adouglas89/Big-Quiet-Fan/dfm v1.0/stl v2/framesecondary_secondarybladeshollow.stl

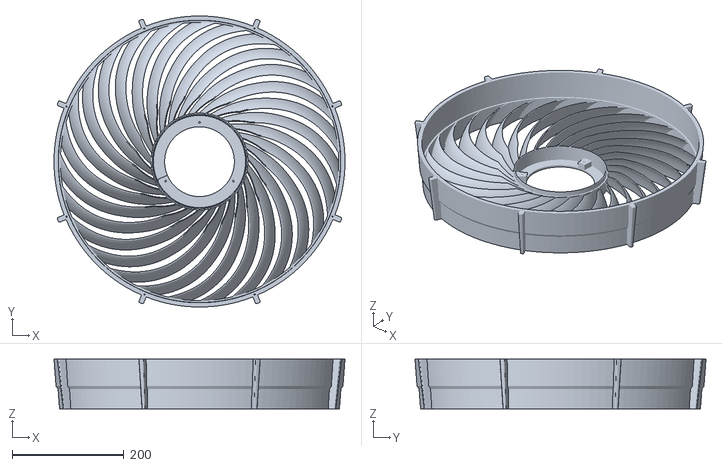
[picture p14: CAD file, 2025-12-09]
dfm v1.0/stl v2/framesecondary_secondarybladeshollow.stl
520.8 x 520.8 x 88.8
