adouglas89/Big-Quiet-Fan/dfm v1.0/trimmedprimarynorim.step

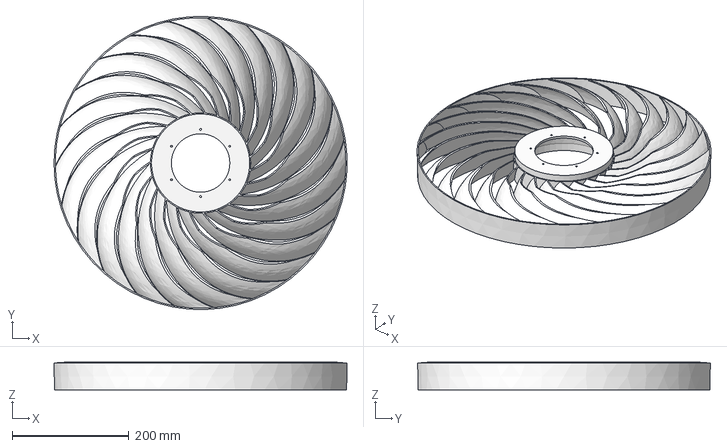
[picture p15: CAD file, 2026-05-13]
dfm v1.0/trimmedprimarynorim.step
502.3 x 502.4 x 47.4 mm
