adouglas89/Big-Quiet-Fan/ul507shortfatfingerprobe.stl

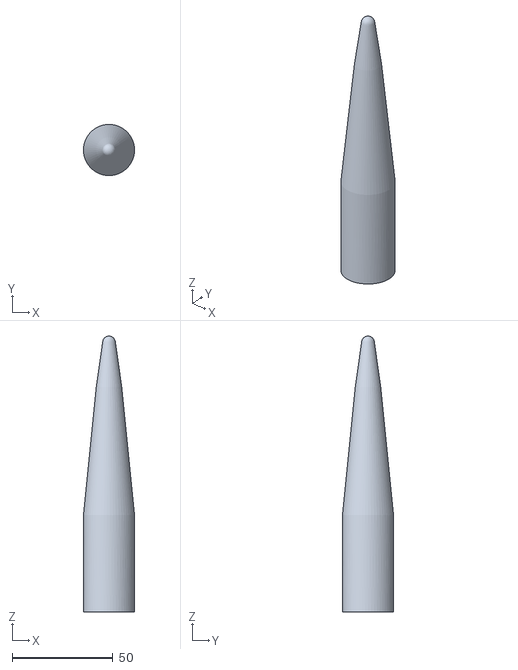
[picture p16: CAD file, 2026-04-09]
ul507shortfatfingerprobe.stl
25.4 x 25.4 x 137.0
