adouglas89/Big-Quiet-Fan/dfm v1.0/primary_thin_blades_norimstillholes.step

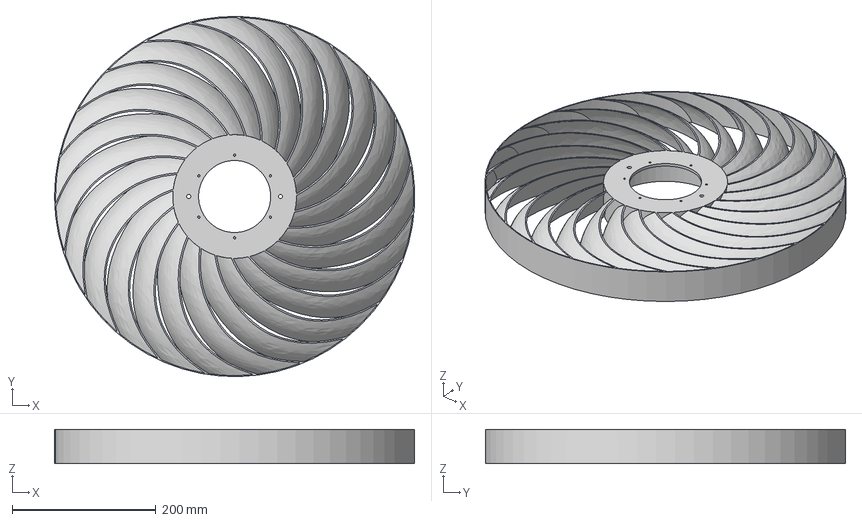
[picture p17: CAD file, 2026-05-13]
dfm v1.0/primary_thin_blades_norimstillholes.step
500.6 x 500.8 x 47.4 mm
