adouglas89/Big-Quiet-Fan/dfm v1.0/prototyping stuff/3mf/finished for kits run june 13 onwards/motor_cover_jayohsblackpetg1.3mf

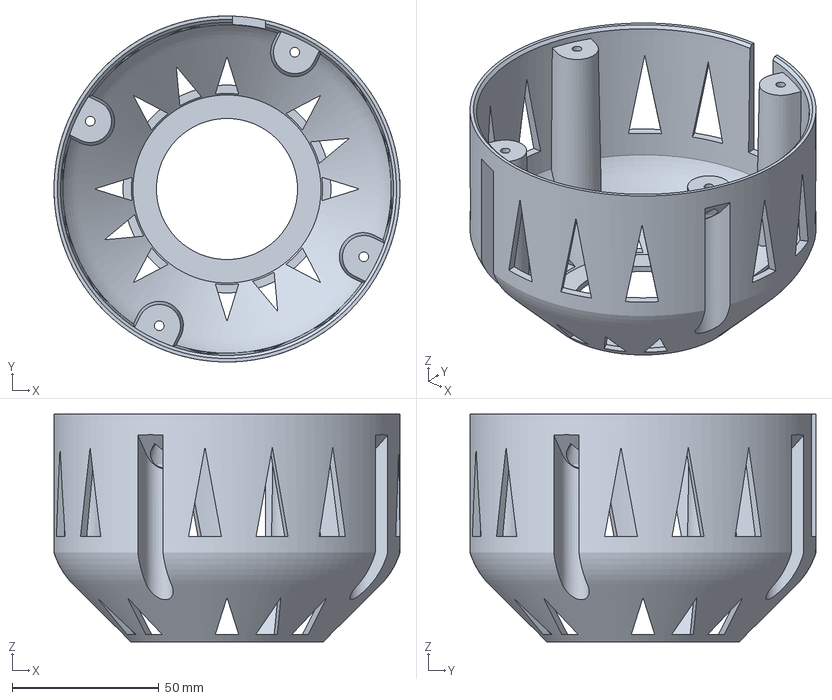
[picture p18: CAD file, 2026-06-17]
dfm v1.0/prototyping stuff/3mf/finished for kits run june 13 onwards/motor_cover_jayohsblackpetg1.3mf
117.7 x 117.7 x 77.5 mm
