adouglas89/Big-Quiet-Fan/dfm v1.0/prototyping stuff/3mf/veho-600/fishnet_clamp_ringtry1-hsjayopet-1mmnozzle-june18_2026.3mf

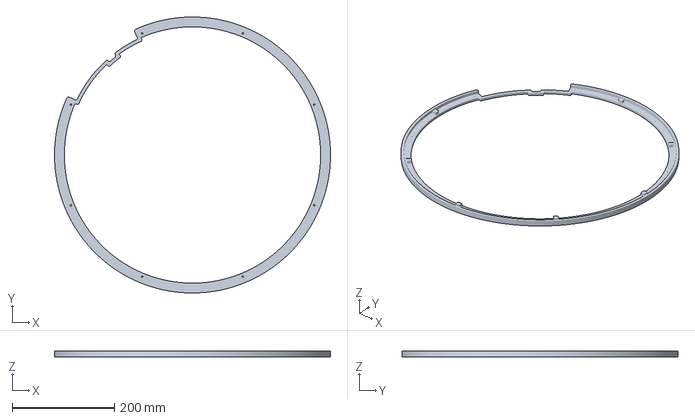
[picture p19: CAD file, 2026-06-18]
dfm v1.0/prototyping stuff/3mf/veho-600/fishnet_clamp_ringtry1-hsjayopet-1mmnozzle-june18_2026.3mf
539.9 x 539.9 x 11.0 mm
