adouglas89/Big-Quiet-Fan/dfm v1.0/prototyping stuff/3mf/veho-600/pretty good/secondary moddedforv-series-1mmnozzle-petgsplit6_wasgood tweakedtravelbeforeretractlimit.3mf

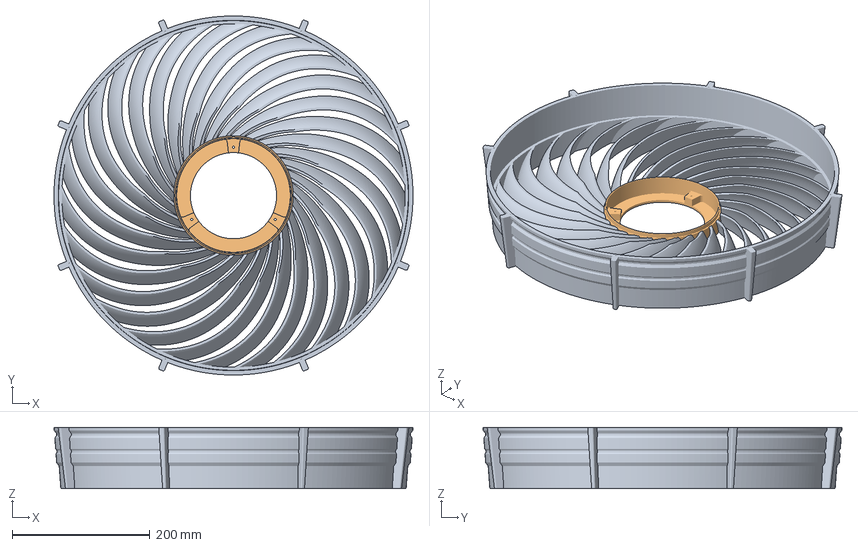
[picture p20: CAD file, 2026-06-16]
dfm v1.0/prototyping stuff/3mf/veho-600/pretty good/secondary moddedforv-series-1mmnozzle-petgsplit6_wasgood tweakedtravelbeforeretractlimit.3mf
520.9 x 520.9 x 88.8 mm
secondary-framesecondaryprintable_outersplittry2.stl
secondary-framesecondaryprintablecentersplittry2.stl
