adouglas89/Big-Quiet-Fan/dfm v1.0/prototyping stuff/stls/new_coupler3/flywheel nointernalholescaptivetype.stl

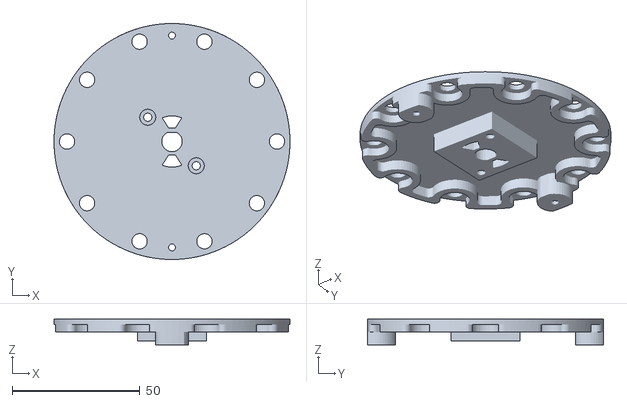
[picture p21: CAD file, 2025-12-23]
dfm v1.0/prototyping stuff/stls/new_coupler3/flywheel nointernalholescaptivetype.stl
92.2 x 92.2 x 10.0
