adouglas89/Big-Quiet-Fan/dfm v1.0/prototyping stuff/stls/simplificationexperiment/plate.stl

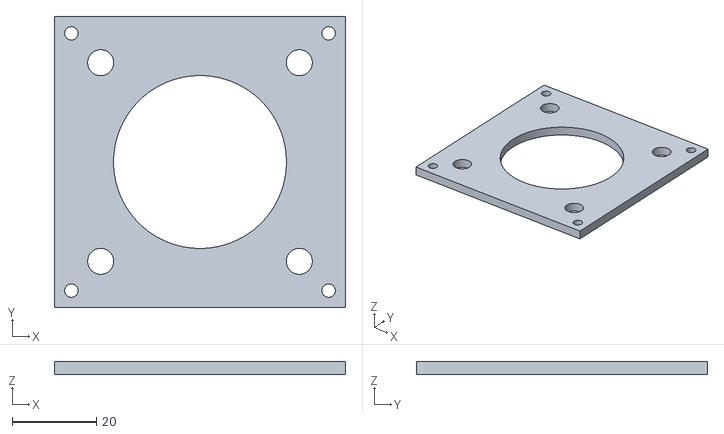
[picture p22: CAD file, 2026-01-07]
dfm v1.0/prototyping stuff/stls/simplificationexperiment/plate.stl
69.0 x 69.0 x 3.00
