adouglas89/Big-Quiet-Fan/dfm v1.0/stl v2/supportblockerfor primary.stl

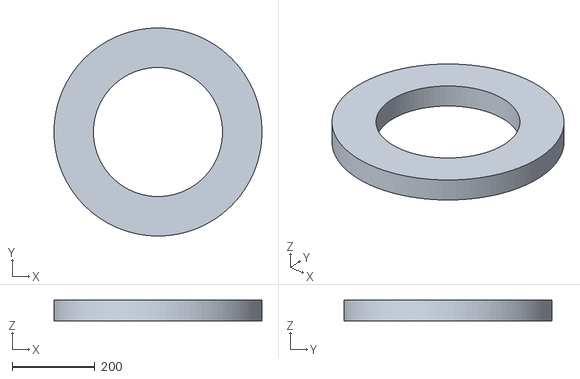
[picture p23: CAD file, 2025-12-06]
dfm v1.0/stl v2/supportblockerfor primary.stl
501.9 x 501.9 x 50.0
