adouglas89/Big-Quiet-Fan/dfm v1.0/prototyping stuff/3mf/finished for kits run june 13 onwards/threearmedcouplerallthreepieces_june15_2026.3mf

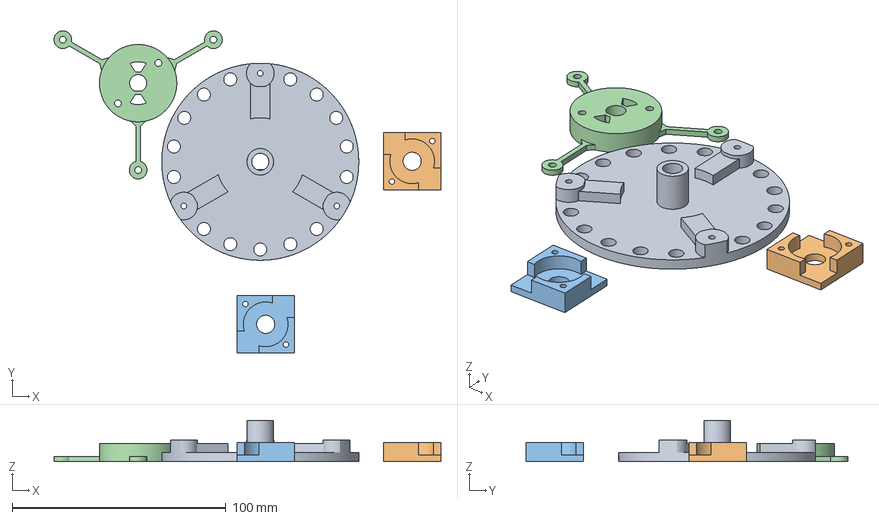
[picture p24: CAD file, 2026-06-17]
dfm v1.0/prototyping stuff/3mf/finished for kits run june 13 onwards/threearmedcouplerallthreepieces_june15_2026.3mf
181.1 x 150.8 x 19.3 mm
bladesideflywheelthreearm.stl
coupler captivething mirror.stl
coupler captivething.stl
motorsidecouplerthreearm9.stl
