adouglas89/Big-Quiet-Fan/dfm v1.0/prototyping stuff/bladetry4.stl

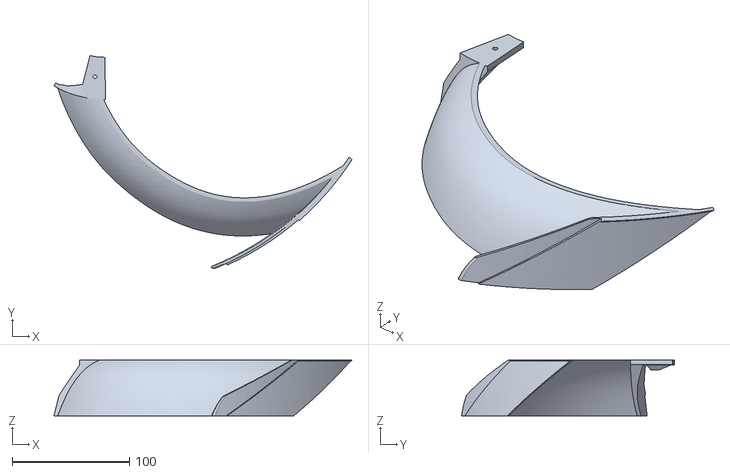
[picture p25: CAD file, 2026-04-09]
dfm v1.0/prototyping stuff/bladetry4.stl
254.3 x 181.6 x 47.4
