adouglas89/Big-Quiet-Fan/dfm v1.0/prototyping stuff/stls/modifierforclamp.stl

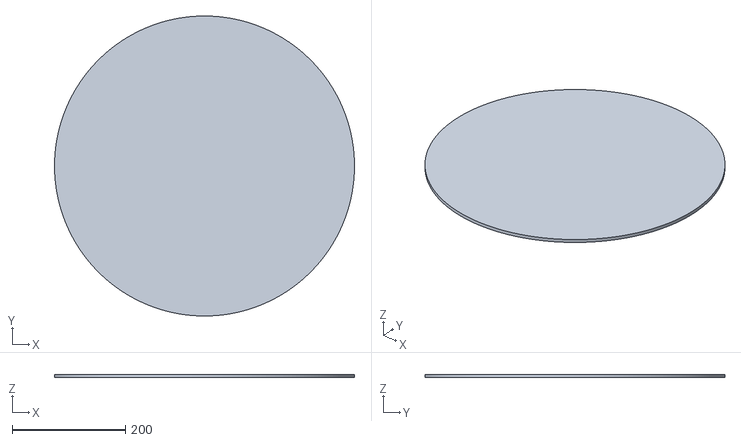
[picture p26: CAD file, 2026-06-18]
dfm v1.0/prototyping stuff/stls/modifierforclamp.stl
529.7 x 529.7 x 6.00
