adouglas89/Big-Quiet-Fan/dfm v1.0/prototyping stuff/stls/simplificationexperiment/pla_motormount.stl

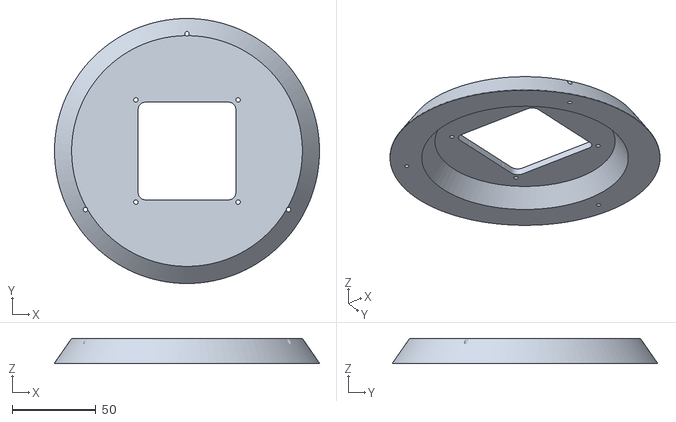
[picture p27: CAD file, 2026-01-07]
dfm v1.0/prototyping stuff/stls/simplificationexperiment/pla_motormount.stl
158.3 x 158.2 x 15.2
