adouglas89/Big-Quiet-Fan/dfm v1.0/prototyping stuff/3mf/finished for kits run june 13 onwards/electronicscoverpetg_0.6_trying to get working3.3mf

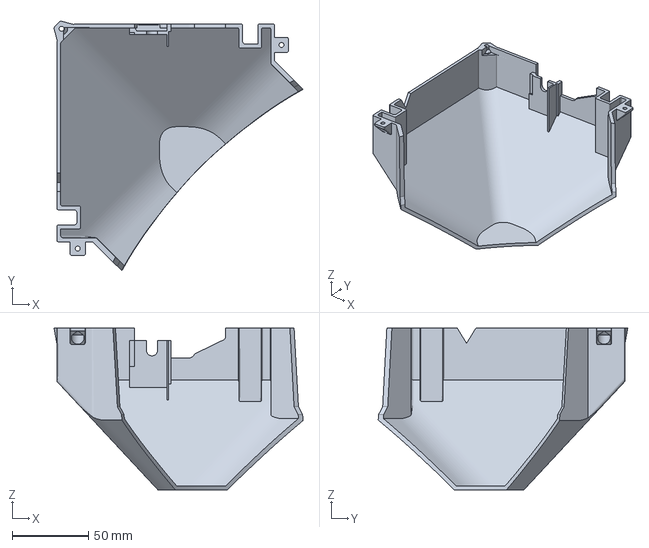
[picture p28: CAD file, 2026-06-17]
dfm v1.0/prototyping stuff/3mf/finished for kits run june 13 onwards/electronicscoverpetg_0.6_trying to get working3.3mf
163.5 x 163.9 x 106.2 mm
