adouglas89/Big-Quiet-Fan/dfm v1.0/prototyping stuff/bladetry9.stl

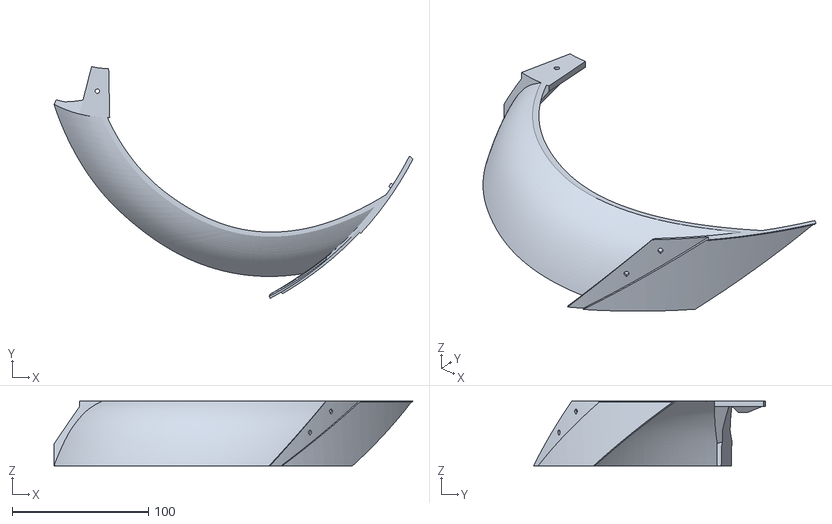
[picture p29: CAD file, 2026-04-09]
dfm v1.0/prototyping stuff/bladetry9.stl
263.4 x 170.1 x 47.4
