adouglas89/Big-Quiet-Fan/dfm v1.0/prototyping stuff/stls/peg5.stl

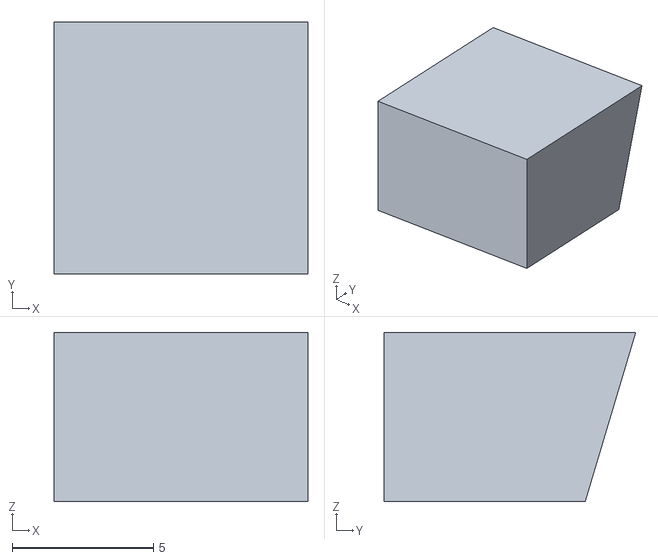
[picture p30: CAD file, 2026-06-18]
dfm v1.0/prototyping stuff/stls/peg5.stl
9.00 x 8.91 x 6.00
