adouglas89/Big-Quiet-Fan/dfm v1.0/prototyping stuff/stls/new_coupler3/backcapturethingcoupler.stl

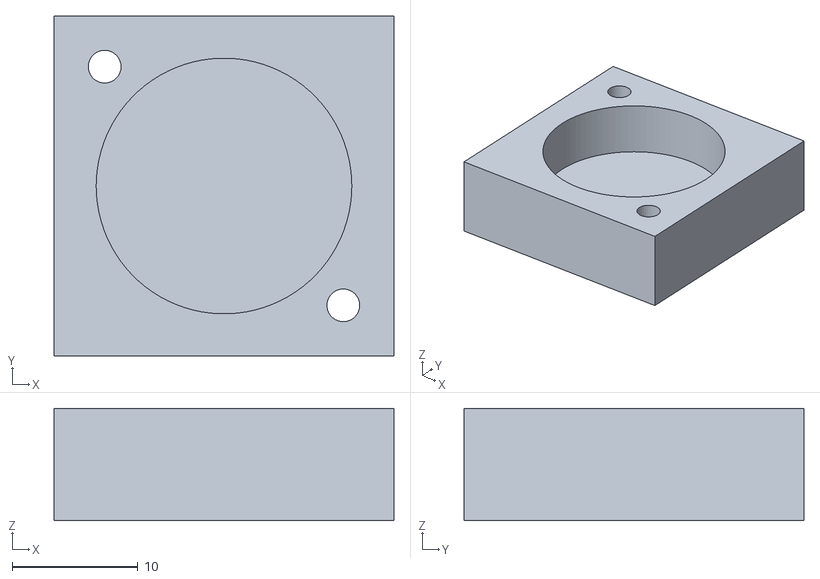
[picture p31: CAD file, 2025-12-23]
dfm v1.0/prototyping stuff/stls/new_coupler3/backcapturethingcoupler.stl
27.0 x 27.0 x 8.90
