adouglas89/Big-Quiet-Fan/dfm v1.0/prototyping stuff/3mf/finished for kits run june 13 onwards/bqfmotorflexure_3x_85A_june15_2026.3mf

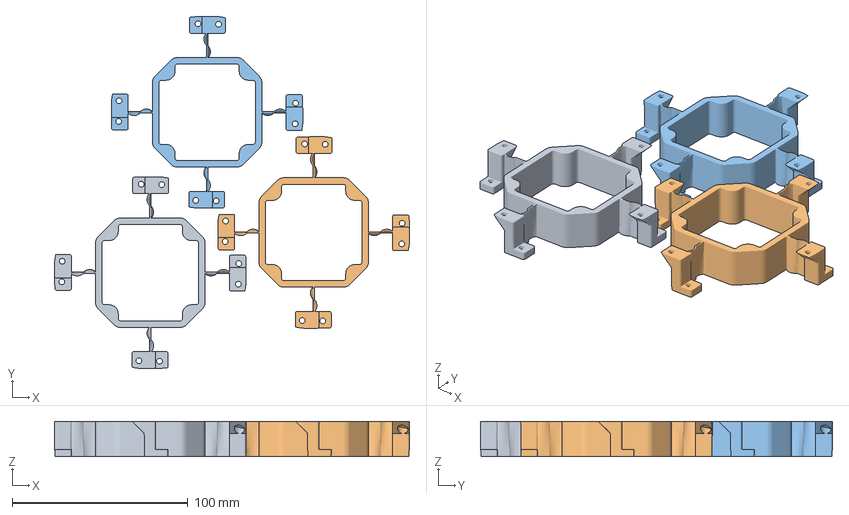
[picture p32: CAD file, 2026-06-16]
dfm v1.0/prototyping stuff/3mf/finished for kits run june 13 onwards/bqfmotorflexure_3x_85A_june15_2026.3mf
202.3 x 200.6 x 20.0 mm
