adouglas89/Big-Quiet-Fan/dfm v1.0/prototyping stuff/3mf/veho-600/primary_middlechoppedaway_upsidedown_trimmed.3mf

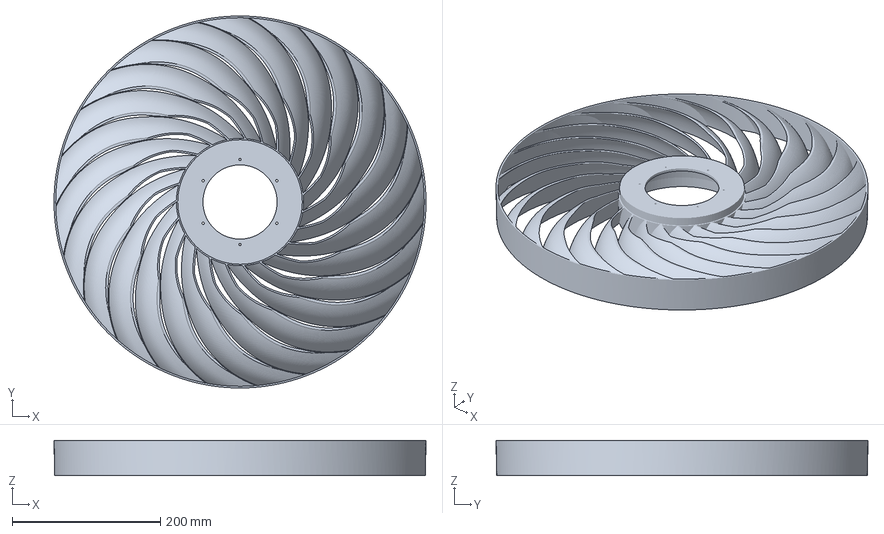
[picture p33: CAD file, 2026-06-16]
dfm v1.0/prototyping stuff/3mf/veho-600/primary_middlechoppedaway_upsidedown_trimmed.3mf
502.6 x 502.6 x 47.4 mm
