adouglas89/Big-Quiet-Fan/dfm v1.0/prototyping stuff/hubtry1.stl

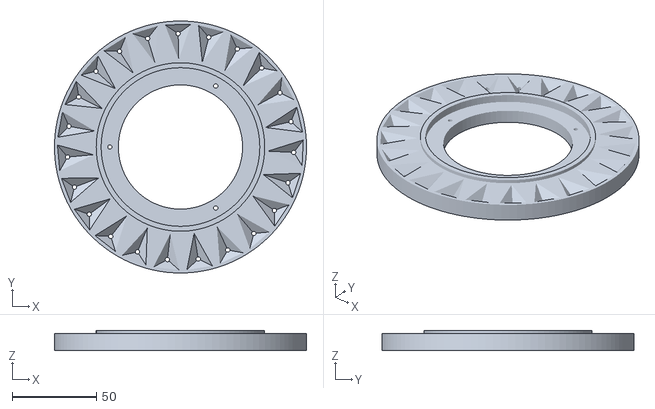
[picture p34: CAD file, 2026-04-09]
dfm v1.0/prototyping stuff/hubtry1.stl
149.3 x 149.3 x 12.0
