adouglas89/Big-Quiet-Fan/dfm v1.0/prototyping stuff/stls/new_coupler3/bladeside.stl

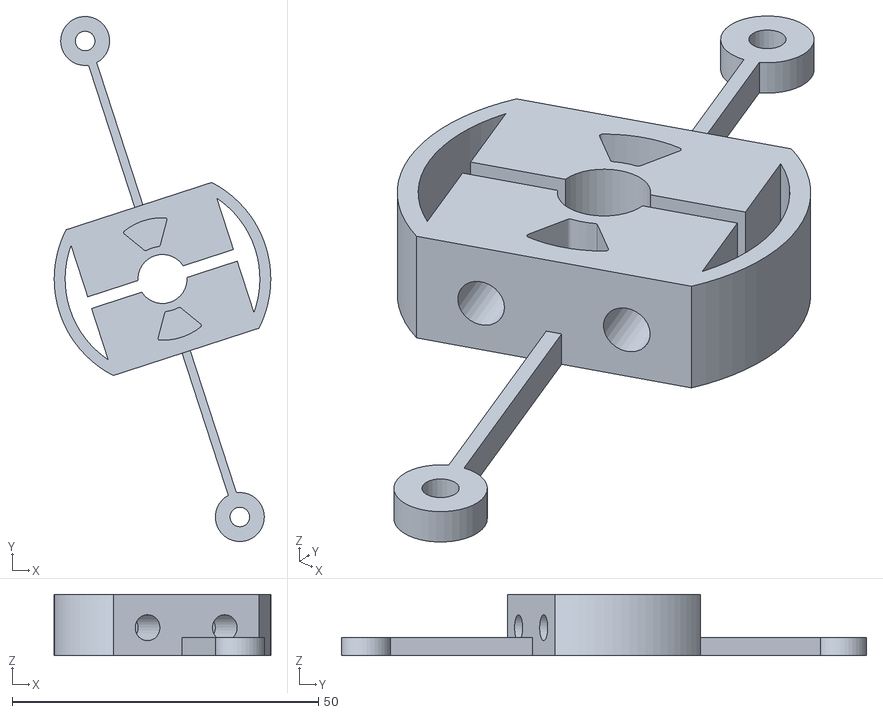
[picture p35: CAD file, 2025-12-23]
dfm v1.0/prototyping stuff/stls/new_coupler3/bladeside.stl
35.4 x 85.7 x 10.0
