adouglas89/Big-Quiet-Fan/dfm v1.0/prototyping stuff/bladetry5.stl

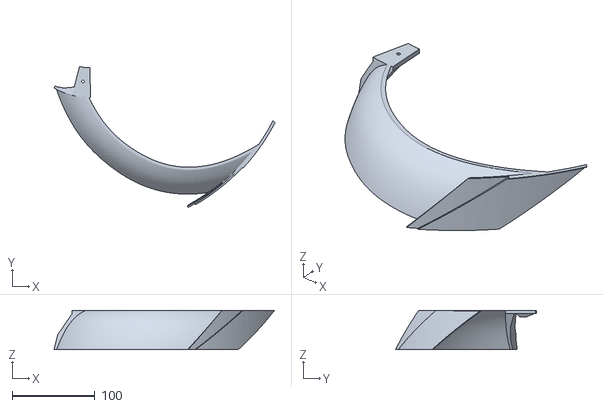
[picture p36: CAD file, 2026-04-09]
dfm v1.0/prototyping stuff/bladetry5.stl
266.5 x 170.1 x 47.4
