adouglas89/Big-Quiet-Fan/dfm v1.0/prototyping stuff/blade.stl

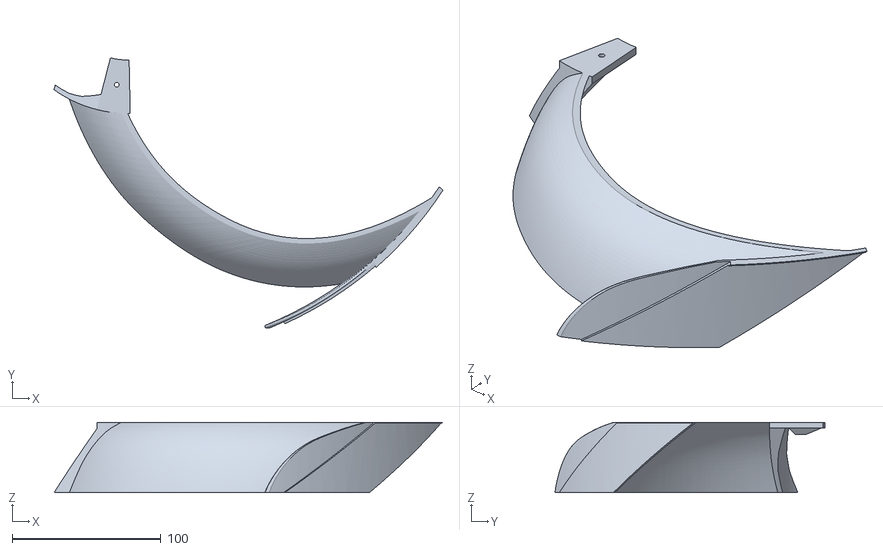
[picture p37: CAD file, 2026-04-09]
dfm v1.0/prototyping stuff/blade.stl
261.5 x 181.6 x 47.4
