adouglas89/Big-Quiet-Fan/dfm v1.0/prototyping stuff/stls/peg3.stl

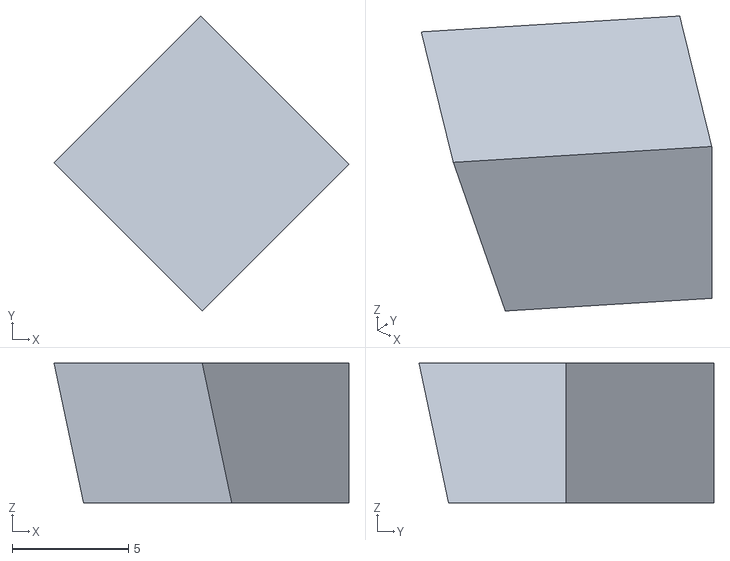
[picture p38: CAD file, 2026-06-18]
dfm v1.0/prototyping stuff/stls/peg3.stl
12.7 x 12.7 x 6.00
