adouglas89/Big-Quiet-Fan/dfm v1.0/prototyping stuff/3mf/electronicscover_petg0_8mm_potrelief.3mf

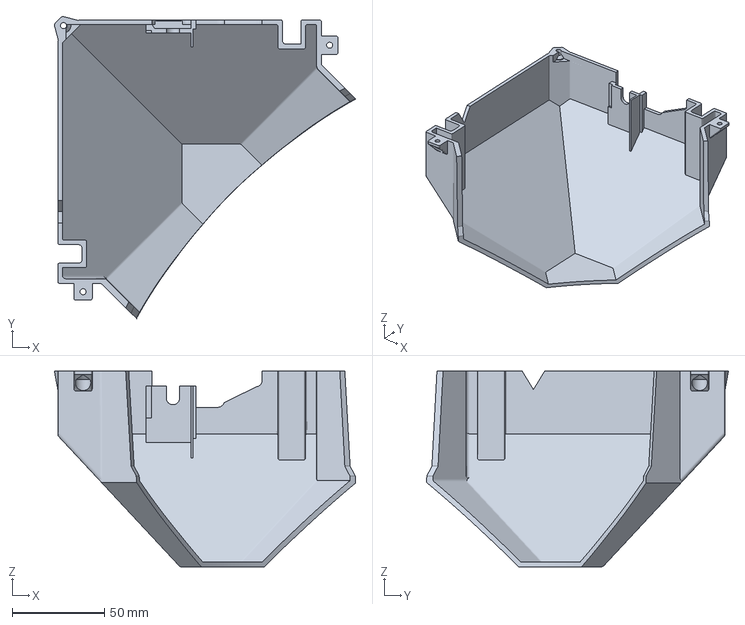
[picture p39: CAD file, 2026-06-16]
dfm v1.0/prototyping stuff/3mf/electronicscover_petg0_8mm_potrelief.3mf
163.5 x 163.9 x 106.2 mm
