adouglas89/Big-Quiet-Fan/dfm v1.0/prototyping stuff/3mf/veho-600/v16p_thin_petg1mmnozzle_thickerlayers.3mf

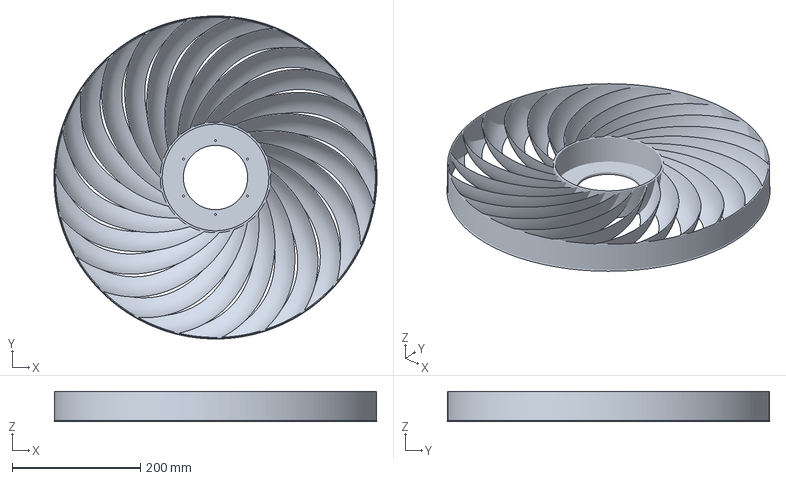
[picture p40: CAD file, 2026-06-16]
dfm v1.0/prototyping stuff/3mf/veho-600/v16p_thin_petg1mmnozzle_thickerlayers.3mf
503.0 x 503.0 x 47.4 mm
