adouglas89/Big-Quiet-Fan/dfm v1.0/prototyping stuff/mangledprimarytry2.stl

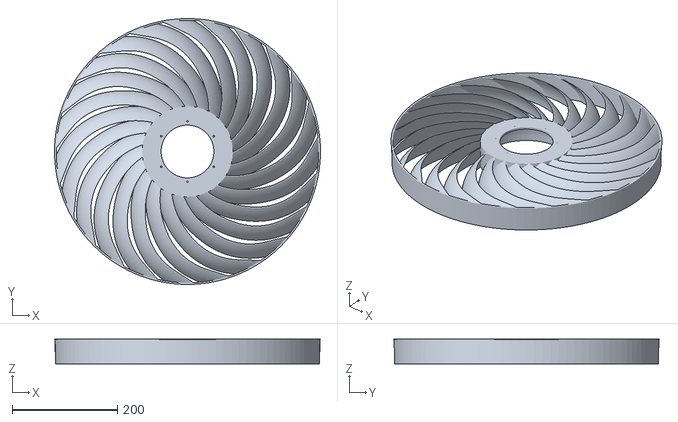
[picture p41: CAD file, 2026-03-26]
dfm v1.0/prototyping stuff/mangledprimarytry2.stl
504.7 x 504.4 x 47.4
