adouglas89/Big-Quiet-Fan/dfm v1.0/prototyping stuff/3mf/electronicscoverpetg_0.6_trying to get working2.3mf

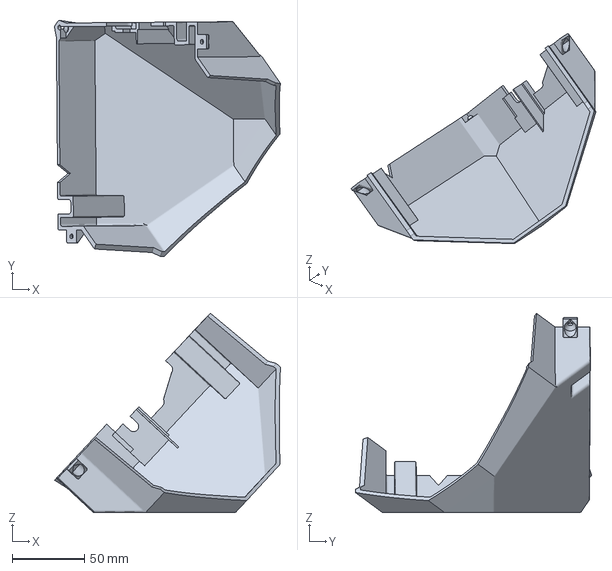
[picture p42: CAD file, 2026-06-16]
dfm v1.0/prototyping stuff/3mf/electronicscoverpetg_0.6_trying to get working2.3mf
156.2 x 163.3 x 137.9 mm
