adouglas89/Big-Quiet-Fan/dfm v1.0/prototyping stuff/3mf/splitblade_center_clamsp_cfpetg_lakegreen.3mf

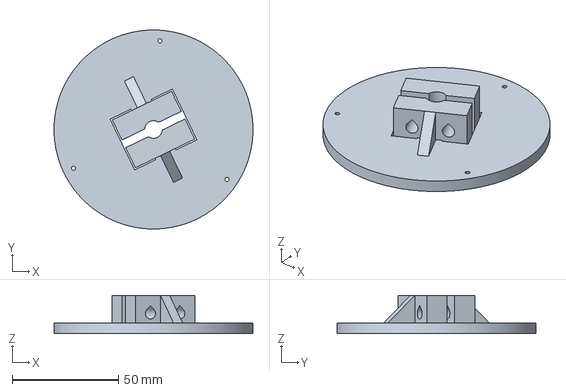
[picture p43: CAD file, 2026-06-16]
dfm v1.0/prototyping stuff/3mf/splitblade_center_clamsp_cfpetg_lakegreen.3mf
93.6 x 93.6 x 18.0 mm
