adouglas89/Big-Quiet-Fan/dfm v1.0/prototyping stuff/stls/pegstry1.stl

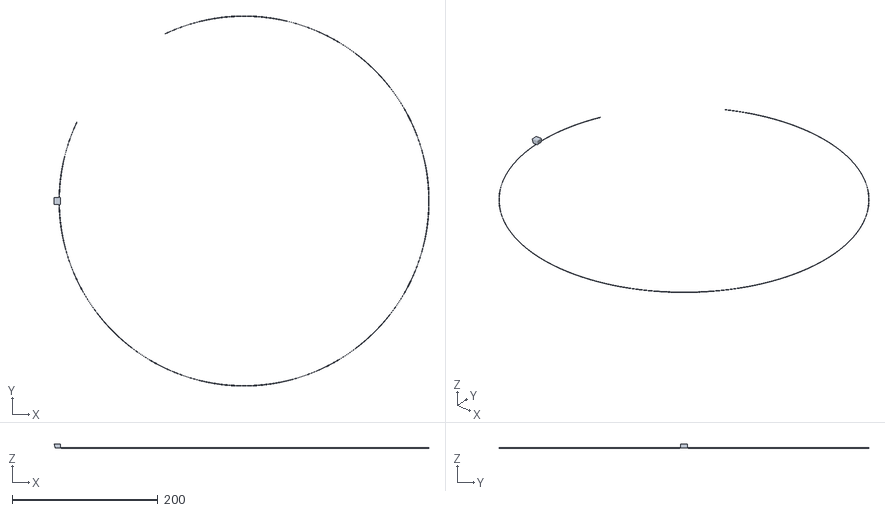
[picture p44: CAD file, 2026-06-18]
dfm v1.0/prototyping stuff/stls/pegstry1.stl
515.3 x 508.3 x 6.00
