adouglas89/Big-Quiet-Fan/dfm v1.0/prototyping stuff/stls/modifierupperpart.stl

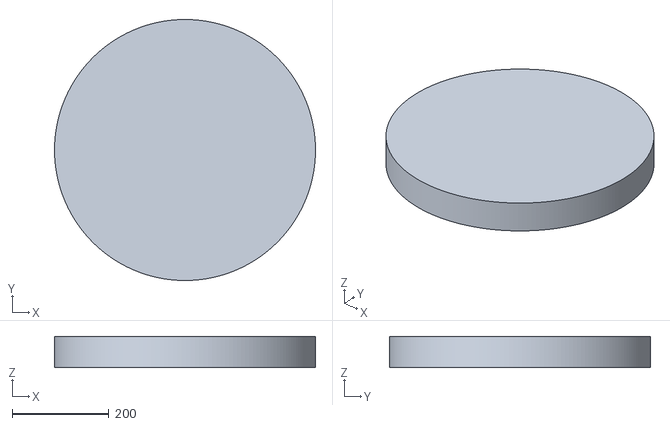
[picture p45: CAD file, 2026-06-17]
dfm v1.0/prototyping stuff/stls/modifierupperpart.stl
539.6 x 539.6 x 64.7
