adouglas89/Big-Quiet-Fan/dfm v1.0/prototyping stuff/3mf/pliersinserttry1.3mf

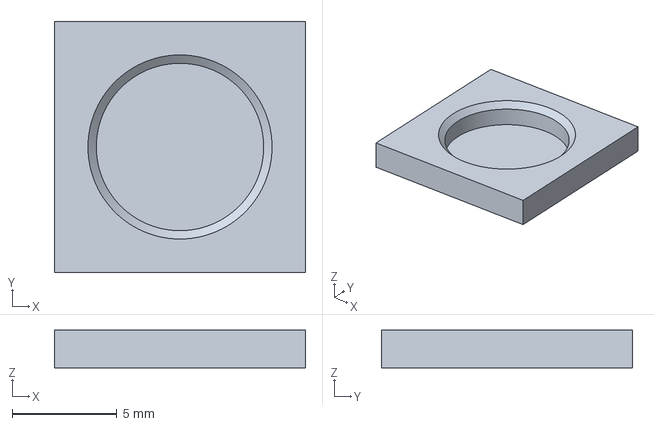
[picture p46: CAD file, 2026-06-16]
dfm v1.0/prototyping stuff/3mf/pliersinserttry1.3mf
12.0 x 12.0 x 1.80 mm
