adouglas89/Big-Quiet-Fan/dfm v1.0/prototyping stuff/stls/motorsidecouplerthreearm_thickenedroot.stl

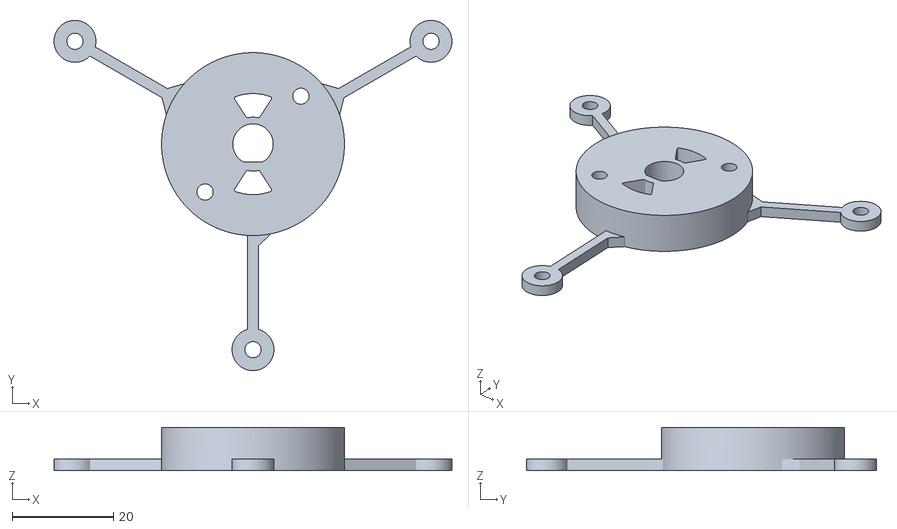
[picture p47: CAD file, 2026-06-16]
dfm v1.0/prototyping stuff/stls/motorsidecouplerthreearm_thickenedroot.stl
78.8 x 69.3 x 8.53
