adouglas89/Big-Quiet-Fan/dfm v1.0/prototyping stuff/stls/secondary-framesecondaryprintable_center_shrunk.stl

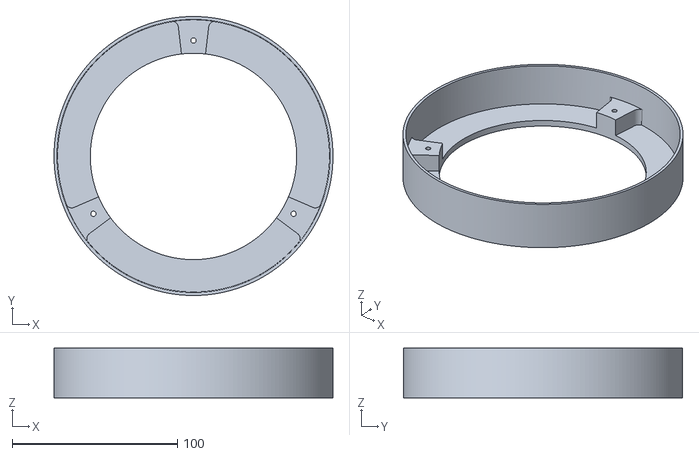
[picture p48: CAD file, 2026-06-16]
dfm v1.0/prototyping stuff/stls/secondary-framesecondaryprintable_center_shrunk.stl
169.0 x 169.0 x 30.2
