adouglas89/Big-Quiet-Fan/dfm v1.0/prototyping stuff/3mf/threearmedcouplerallthreepieces.3mf

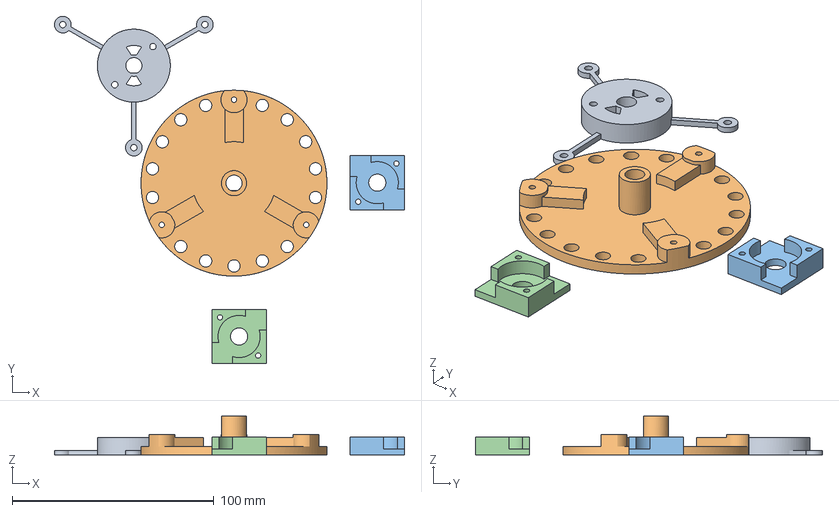
[picture p49: CAD file, 2026-06-16]
dfm v1.0/prototyping stuff/3mf/threearmedcouplerallthreepieces.3mf
173.6 x 172.3 x 19.3 mm
threearmbladesidecorrected.stl
bladesideflywheelthreearm.stl
coupler captivething mirror.stl
coupler captivething.stl
