adouglas89/Big-Quiet-Fan/dfm v1.0/prototyping stuff/stls/modifierforcenterstrength.stl

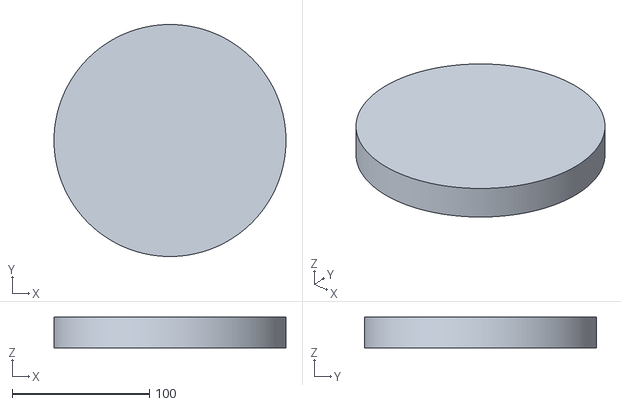
[picture p50: CAD file, 2026-06-16]
dfm v1.0/prototyping stuff/stls/modifierforcenterstrength.stl
169.1 x 169.1 x 22.4
