adouglas89/Big-Quiet-Fan/dfm v1.0/prototyping stuff/3mf/veho-600/secondary_center_thickerforvseries.3mf

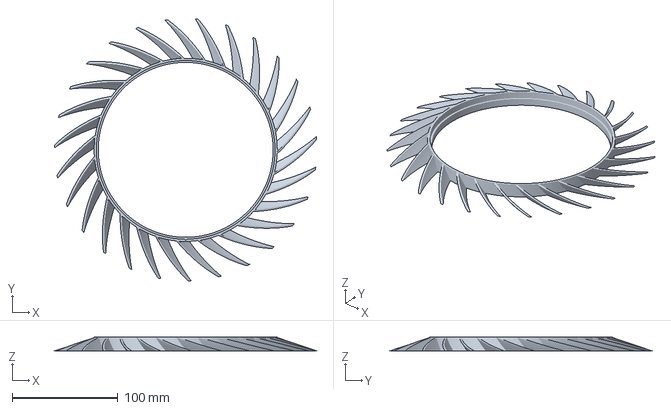
[picture p51: CAD file, 2026-05-19]
dfm v1.0/prototyping stuff/3mf/veho-600/secondary_center_thickerforvseries.3mf
248.0 x 248.1 x 13.0 mm
