adouglas89/Big-Quiet-Fan/dfm v1.0/prototyping stuff/stls/pliersinserttry6.stl

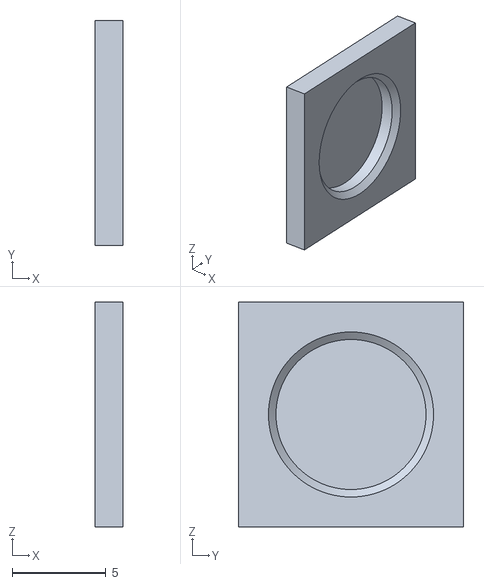
[picture p52: CAD file, 2026-06-16]
dfm v1.0/prototyping stuff/stls/pliersinserttry6.stl
1.50 x 12.0 x 12.0
