adouglas89/Big-Quiet-Fan/dfm v1.0/prototyping stuff/3mf/shaft_clamp_infilled_petgcf_justone.3mf

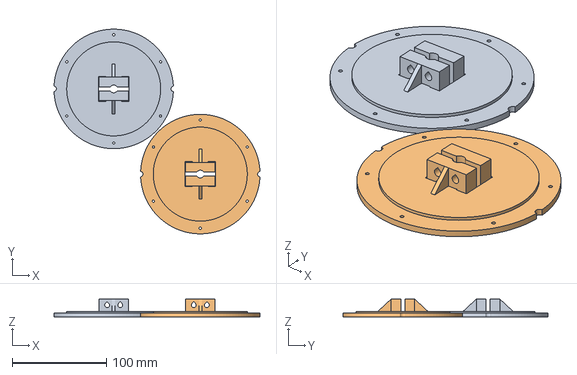
[picture p53: CAD file, 2026-06-16]
dfm v1.0/prototyping stuff/3mf/shaft_clamp_infilled_petgcf_justone.3mf
218.7 x 217.3 x 19.0 mm
