adouglas89/Big-Quiet-Fan/dfm v1.0/prototyping stuff/3mf/splitbladetry2hubouterside.3mf

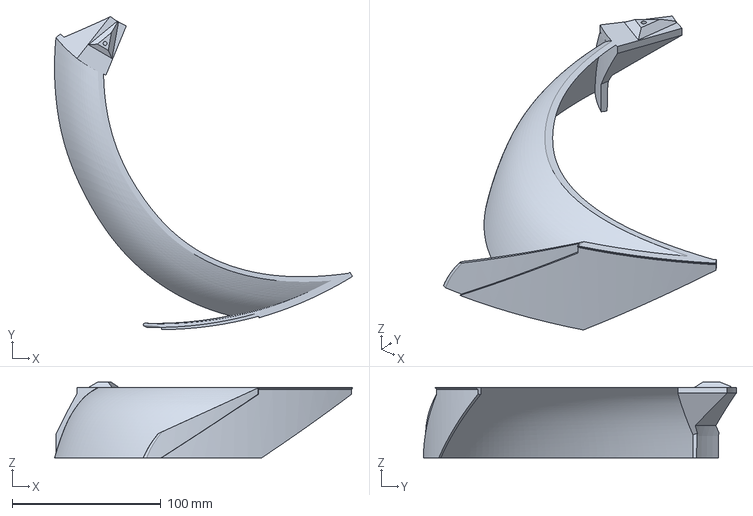
[picture p54: CAD file, 2026-05-13]
dfm v1.0/prototyping stuff/3mf/splitbladetry2hubouterside.3mf
200.5 x 210.8 x 50.8 mm
