adouglas89/Big-Quiet-Fan/dfm v1.0/prototyping stuff/3mf/hardbearingcushions.3mf

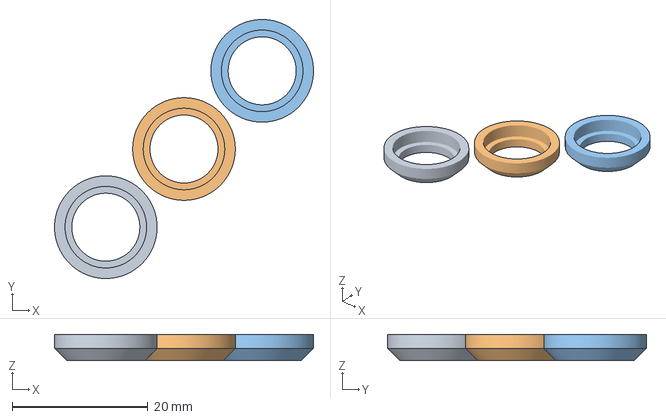
[picture p55: CAD file, 2026-05-13]
dfm v1.0/prototyping stuff/3mf/hardbearingcushions.3mf
38.1 x 38.1 x 3.86 mm
