adouglas89/Big-Quiet-Fan/dfm v1.0/prototyping stuff/3mf/veho-600/secondarycentertrimmedmore with infill.3mf

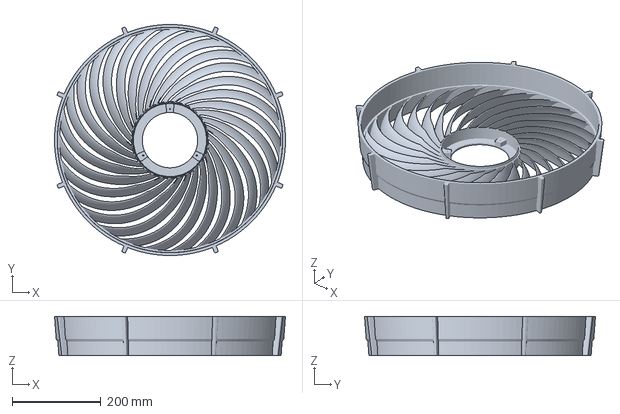
[picture p56: CAD file, 2026-05-13]
dfm v1.0/prototyping stuff/3mf/veho-600/secondarycentertrimmedmore with infill.3mf
520.8 x 520.8 x 88.8 mm
