adouglas89/Big-Quiet-Fan/dfm v1.0/prototyping stuff/stls/pliersinserttry5.stl

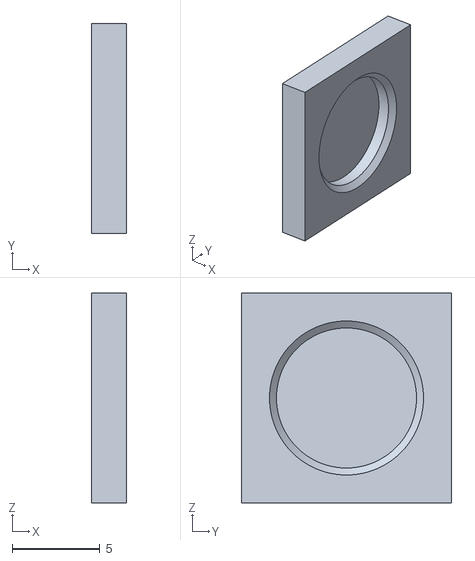
[picture p57: CAD file, 2026-06-16]
dfm v1.0/prototyping stuff/stls/pliersinserttry5.stl
2.00 x 12.0 x 12.0
