adouglas89/Big-Quiet-Fan/dfm v1.0/prototyping stuff/3mf/coupler_flywheel_captivethingbatch1_95A.3mf

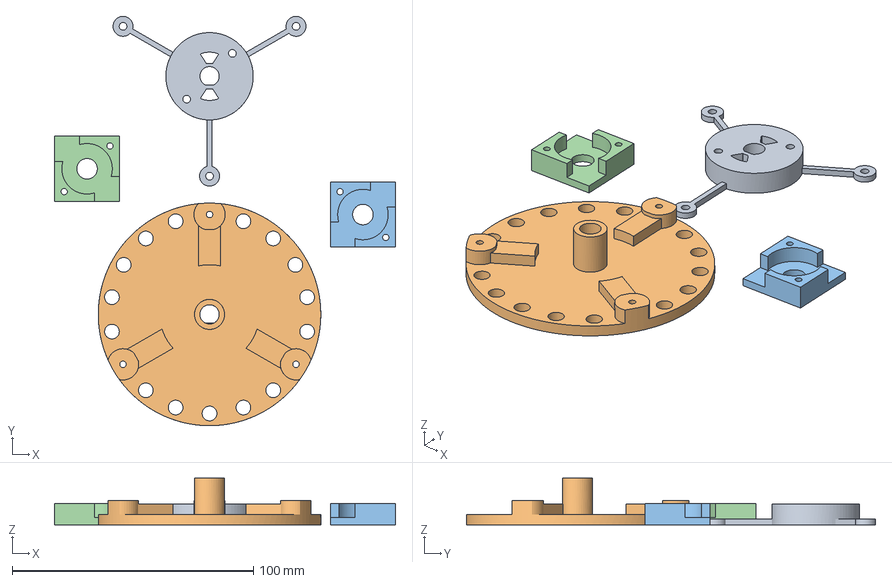
[picture p58: CAD file, 2026-05-13]
dfm v1.0/prototyping stuff/3mf/coupler_flywheel_captivethingbatch1_95A.3mf
141.3 x 169.6 x 19.3 mm
captivebladesidecoupler three arms.stl
bladesideflywheelthreearm.stl
captivething (1)three arms.stl
coupler captivething mirror.stl
