adouglas89/Big-Quiet-Fan/dfm v1.0/prototyping stuff/stls/secondary-framesecondaryprintable_centertry2.stl

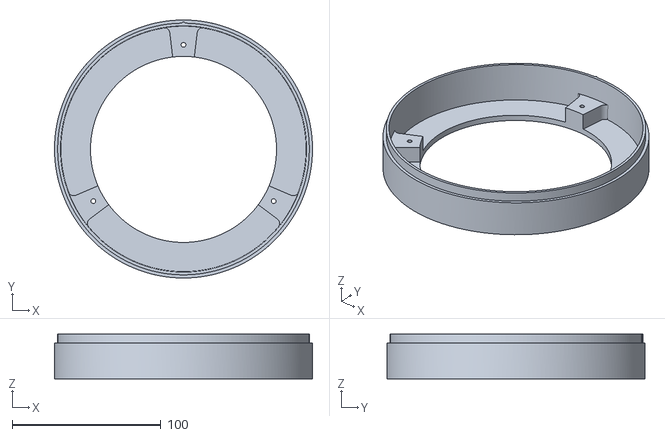
[picture p59: CAD file, 2026-06-16]
dfm v1.0/prototyping stuff/stls/secondary-framesecondaryprintable_centertry2.stl
173.4 x 173.4 x 30.2
