adouglas89/Big-Quiet-Fan/dfm v1.0/prototyping stuff/3mf/veho-600/secondary_centertry1_thick_petg.3mf

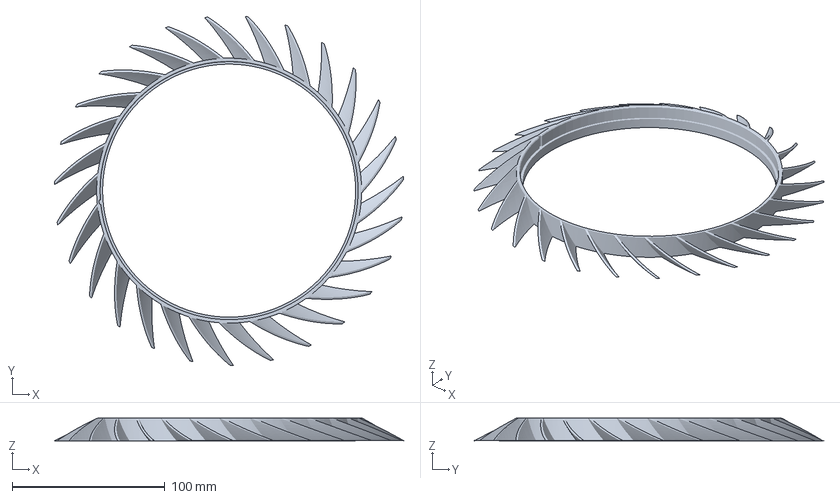
[picture p60: CAD file, 2026-03-18]
dfm v1.0/prototyping stuff/3mf/veho-600/secondary_centertry1_thick_petg.3mf
228.6 x 228.4 x 15.0 mm
