adouglas89/Big-Quiet-Fan/dfm v1.0/prototyping stuff/3mf/splitbladetry2hubouterside_hub.3mf

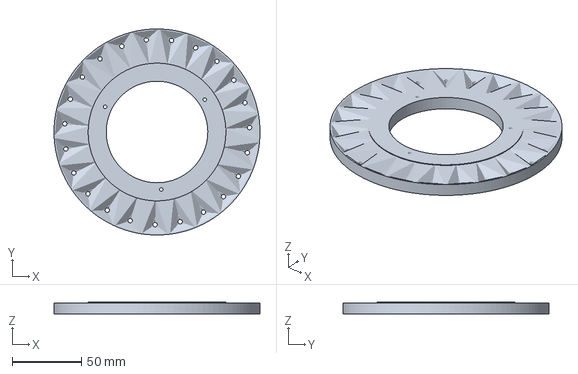
[picture p61: CAD file, 2026-05-13]
dfm v1.0/prototyping stuff/3mf/splitbladetry2hubouterside_hub.3mf
149.3 x 149.3 x 8.42 mm
