adouglas89/Big-Quiet-Fan/dfm v1.0/prototyping stuff/3mf/veho-600/squaregrille3_69mm.3mf

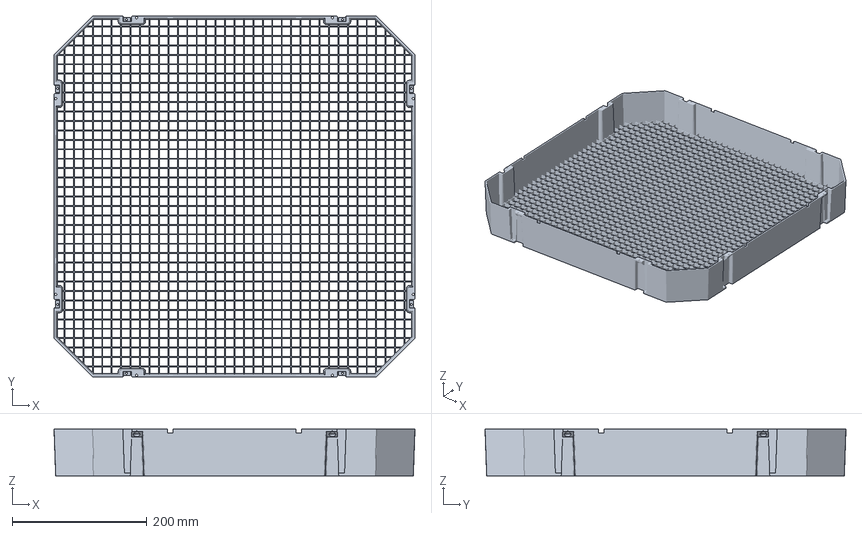
[picture p62: CAD file, 2026-02-25]
dfm v1.0/prototyping stuff/3mf/veho-600/squaregrille3_69mm.3mf
535.0 x 535.0 x 69.0 mm
