adouglas89/Big-Quiet-Fan/dfm v1.0/prototyping stuff/3mf/veho-600/plate3.3mf

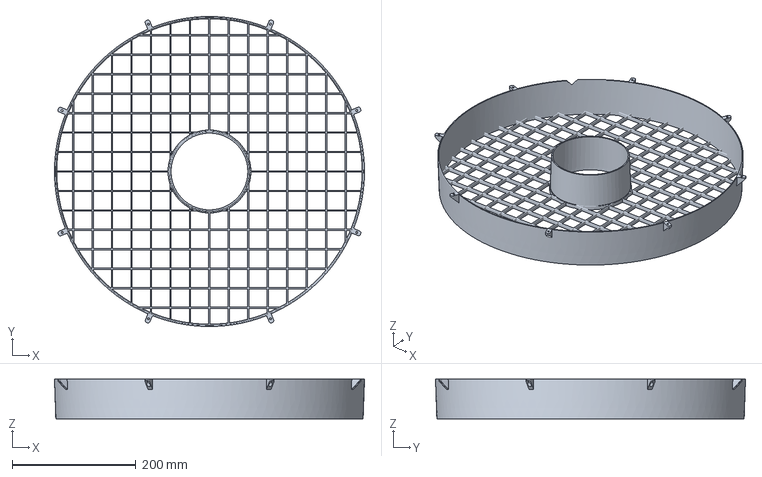
[picture p63: CAD file, 2026-01-31]
dfm v1.0/prototyping stuff/3mf/veho-600/plate3.3mf
501.1 x 501.0 x 63.9 mm
