adouglas89/Big-Quiet-Fan/dfm v1.0/prototyping stuff/3mf/splitbladetry1.3mf

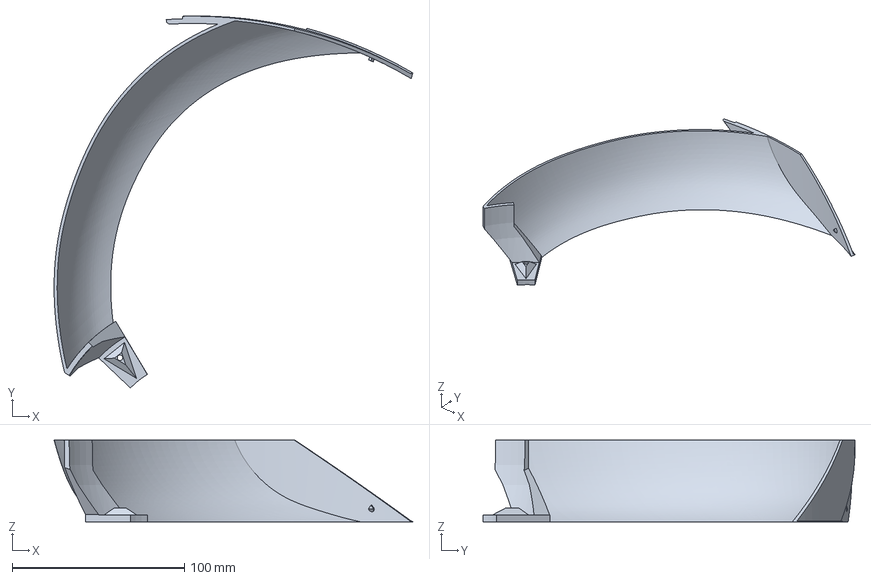
[picture p64: CAD file, 2026-04-09]
dfm v1.0/prototyping stuff/3mf/splitbladetry1.3mf
208.1 x 215.7 x 47.4 mm
