adouglas89/Big-Quiet-Fan/dfm v1.0/prototyping stuff/stls/bladesmodifier2.stl

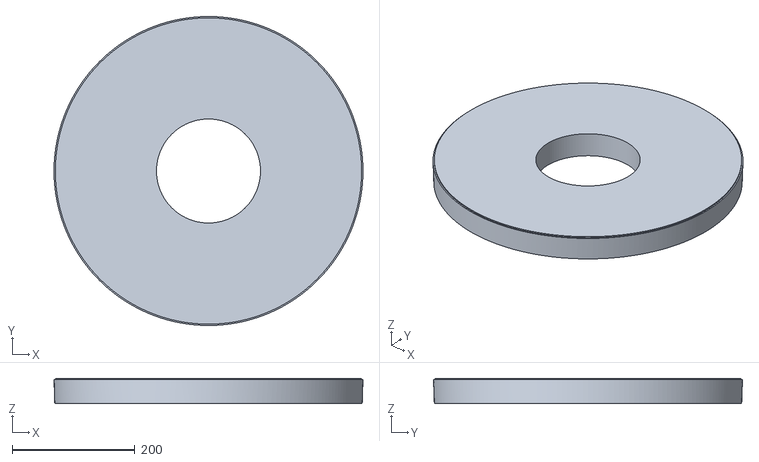
[picture p65: CAD file, 2026-06-16]
dfm v1.0/prototyping stuff/stls/bladesmodifier2.stl
502.4 x 502.5 x 41.0
