adouglas89/Big-Quiet-Fan/dfm v1.0/prototyping stuff/stls/thickernewsecondarymiddle1.stl

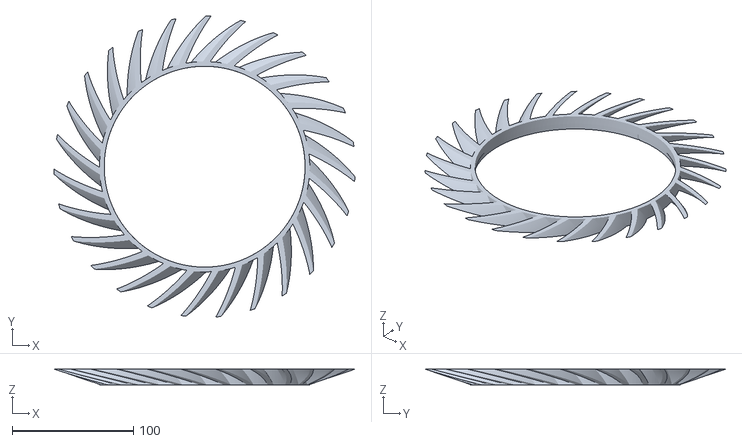
[picture p67: CAD file, 2026-05-19]
dfm v1.0/prototyping stuff/stls/thickernewsecondarymiddle1.stl
248.1 x 248.1 x 13.0
