adouglas89/Big-Quiet-Fan/dfm v1.0/prototyping stuff/3mf/veho-600/v16p_centertry1_thin.3mf

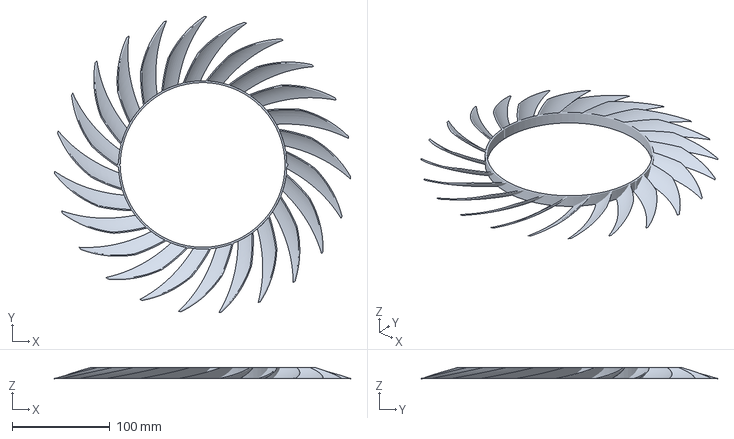
[picture p68: CAD file, 2026-01-31]
dfm v1.0/prototyping stuff/3mf/veho-600/v16p_centertry1_thin.3mf
303.0 x 302.6 x 11.4 mm
