adouglas89/Big-Quiet-Fan/dfm v1.0/prototyping stuff/3mf/veho-600/grille4squaretry1.3mf

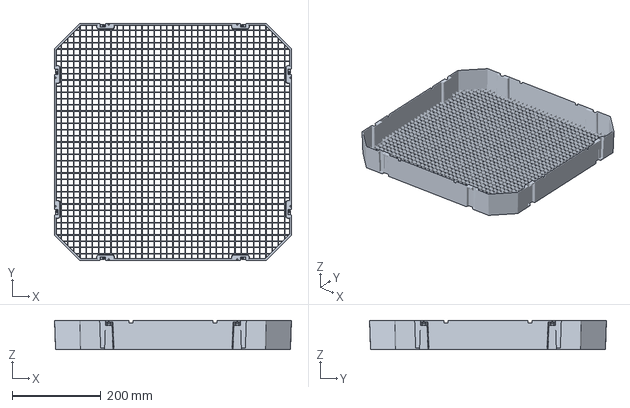
[picture p69: CAD file, 2026-01-31]
dfm v1.0/prototyping stuff/3mf/veho-600/grille4squaretry1.3mf
535.0 x 535.0 x 66.0 mm
