adouglas89/Big-Quiet-Fan/dfm v1.0/main stuff for use by others/main manufacturing files/drawings for manufacture/secondary-frame.pdf

530 | 290 Ø140 Ø3.2 Ø515.22 Ø125 specified. unless otherwise positions are 40 micons All tolerances and hole | Ø168.8+.02 ⁻.07

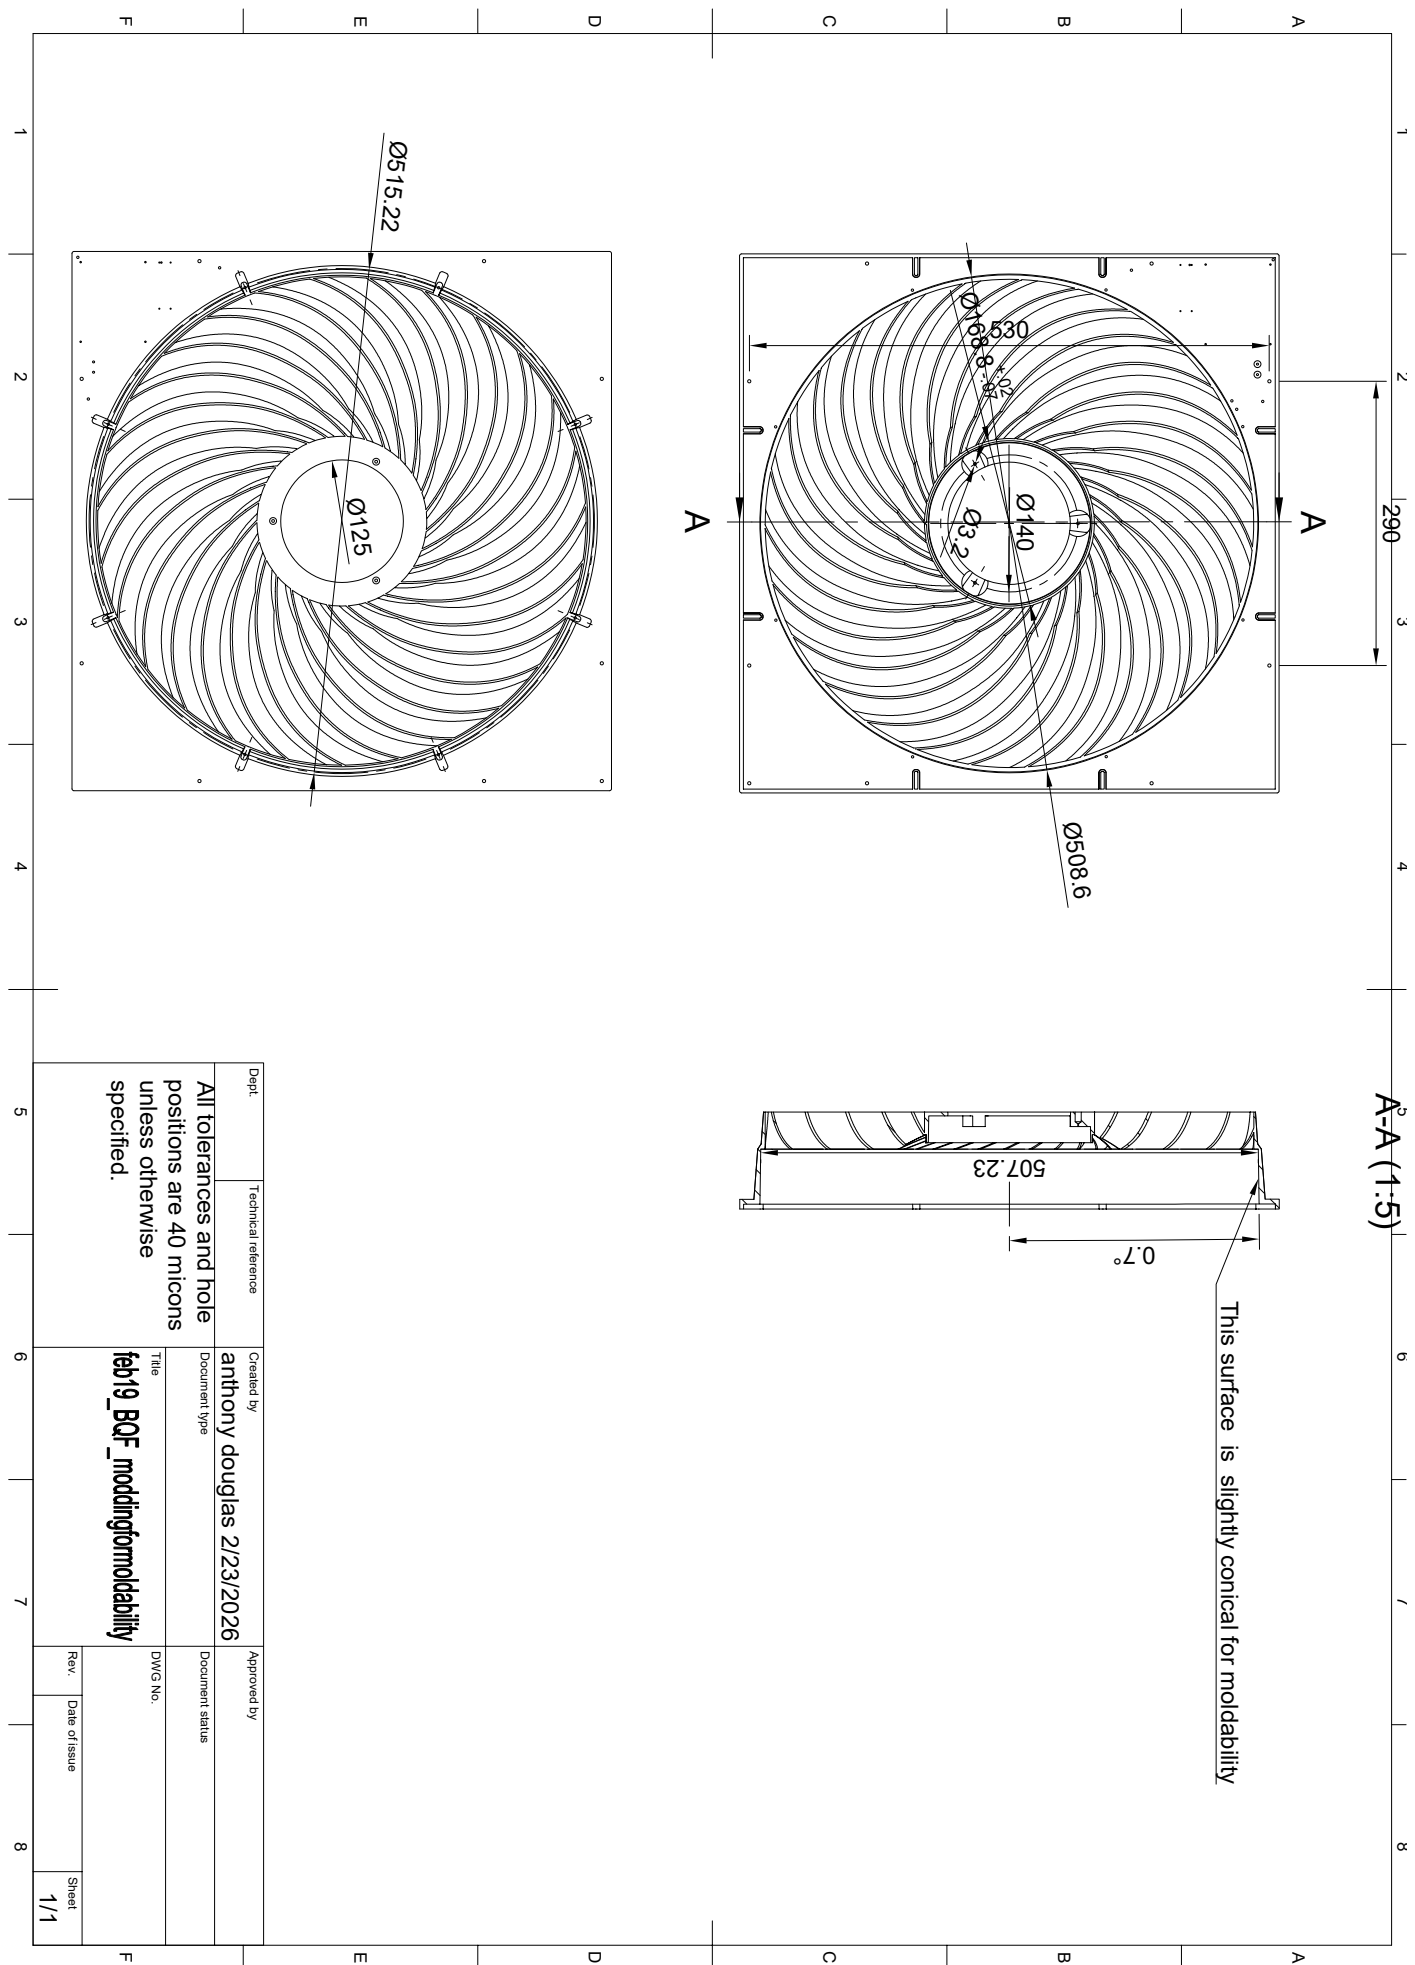
[picture p72: page 1]

1 A 2 3 4 5 6 7 8 1 2 3 4 5 6 7 8 FEDCB FEDCBA Dept. Technical reference Created by Approved by Title DWG No. Document type Document status Rev. Date of issue Sheet 2/23/2026 1/1 anthony douglas AA A-A (1:5)
