adouglas89/Big-Quiet-Fan/dfm v1.0/main stuff for use by others/main manufacturing files/drawings for manufacture/spider coupler half.pdf

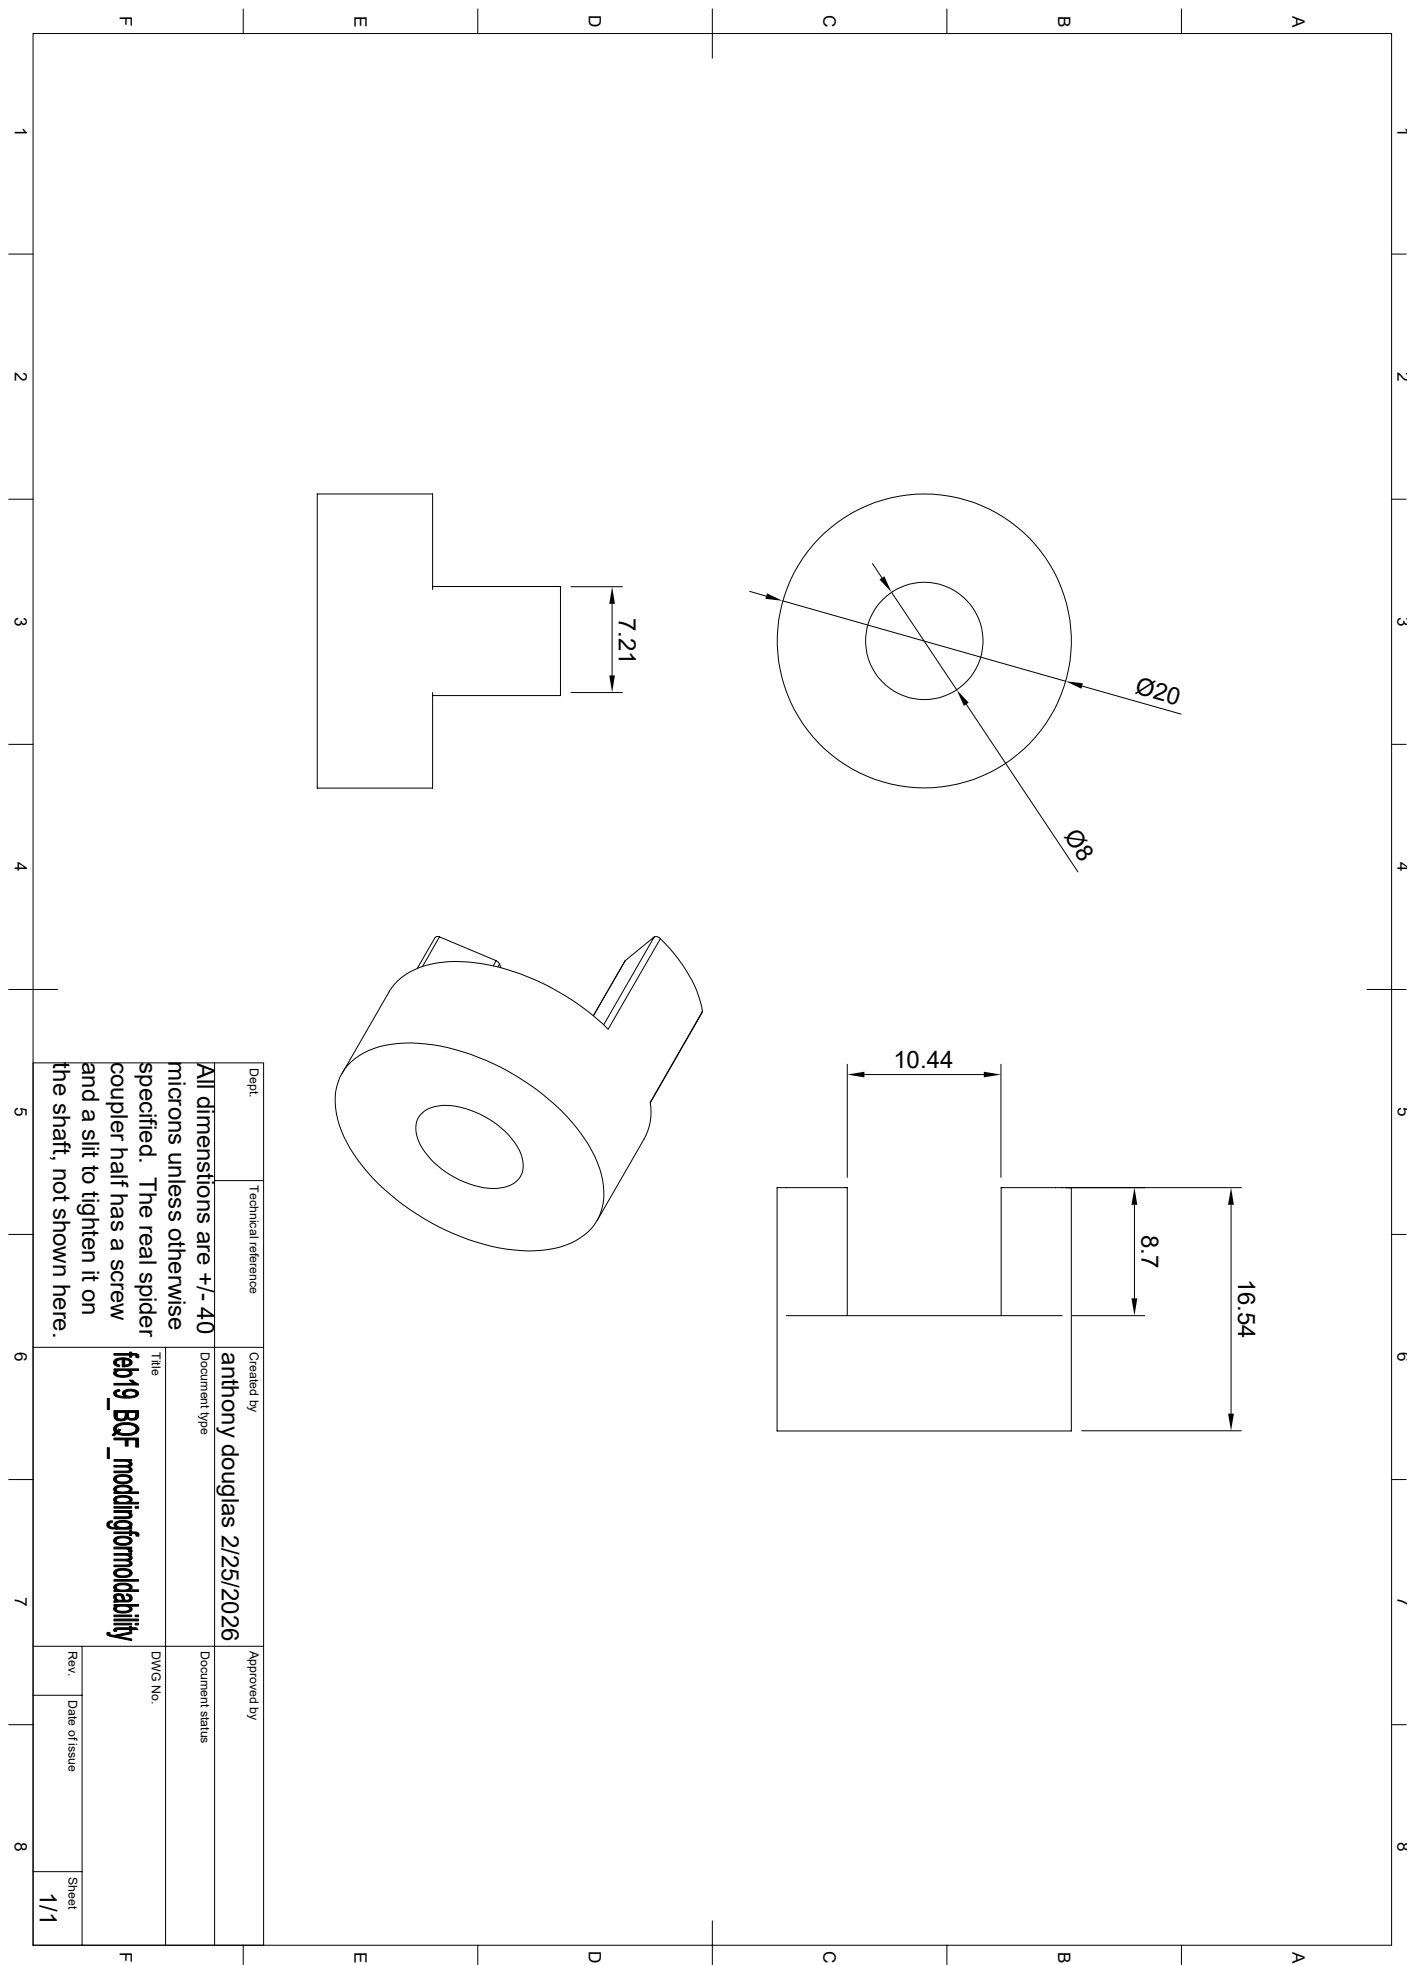
[picture p73: page 1]
16.54 the shaft, not shown here. and a slit to tighten it on coupler half has a screw specified. The real spider microns unless otherwise All dimenstions are +/- 40

1 A 2 3 4 5 6 7 8 1 2 3 4 5 6 7 8 FEDCB FEDCBA Dept. Technical reference Created by Approved by Title DWG No. Document type Document status Rev. Date of issue Sheet 2/25/2026 1/1 anthony douglas Ø8 Ø20
