adouglas89/Big-Quiet-Fan/dfm v1.0/main stuff for use by others/main manufacturing files/drawings for manufacture/shaft clamp.pdf

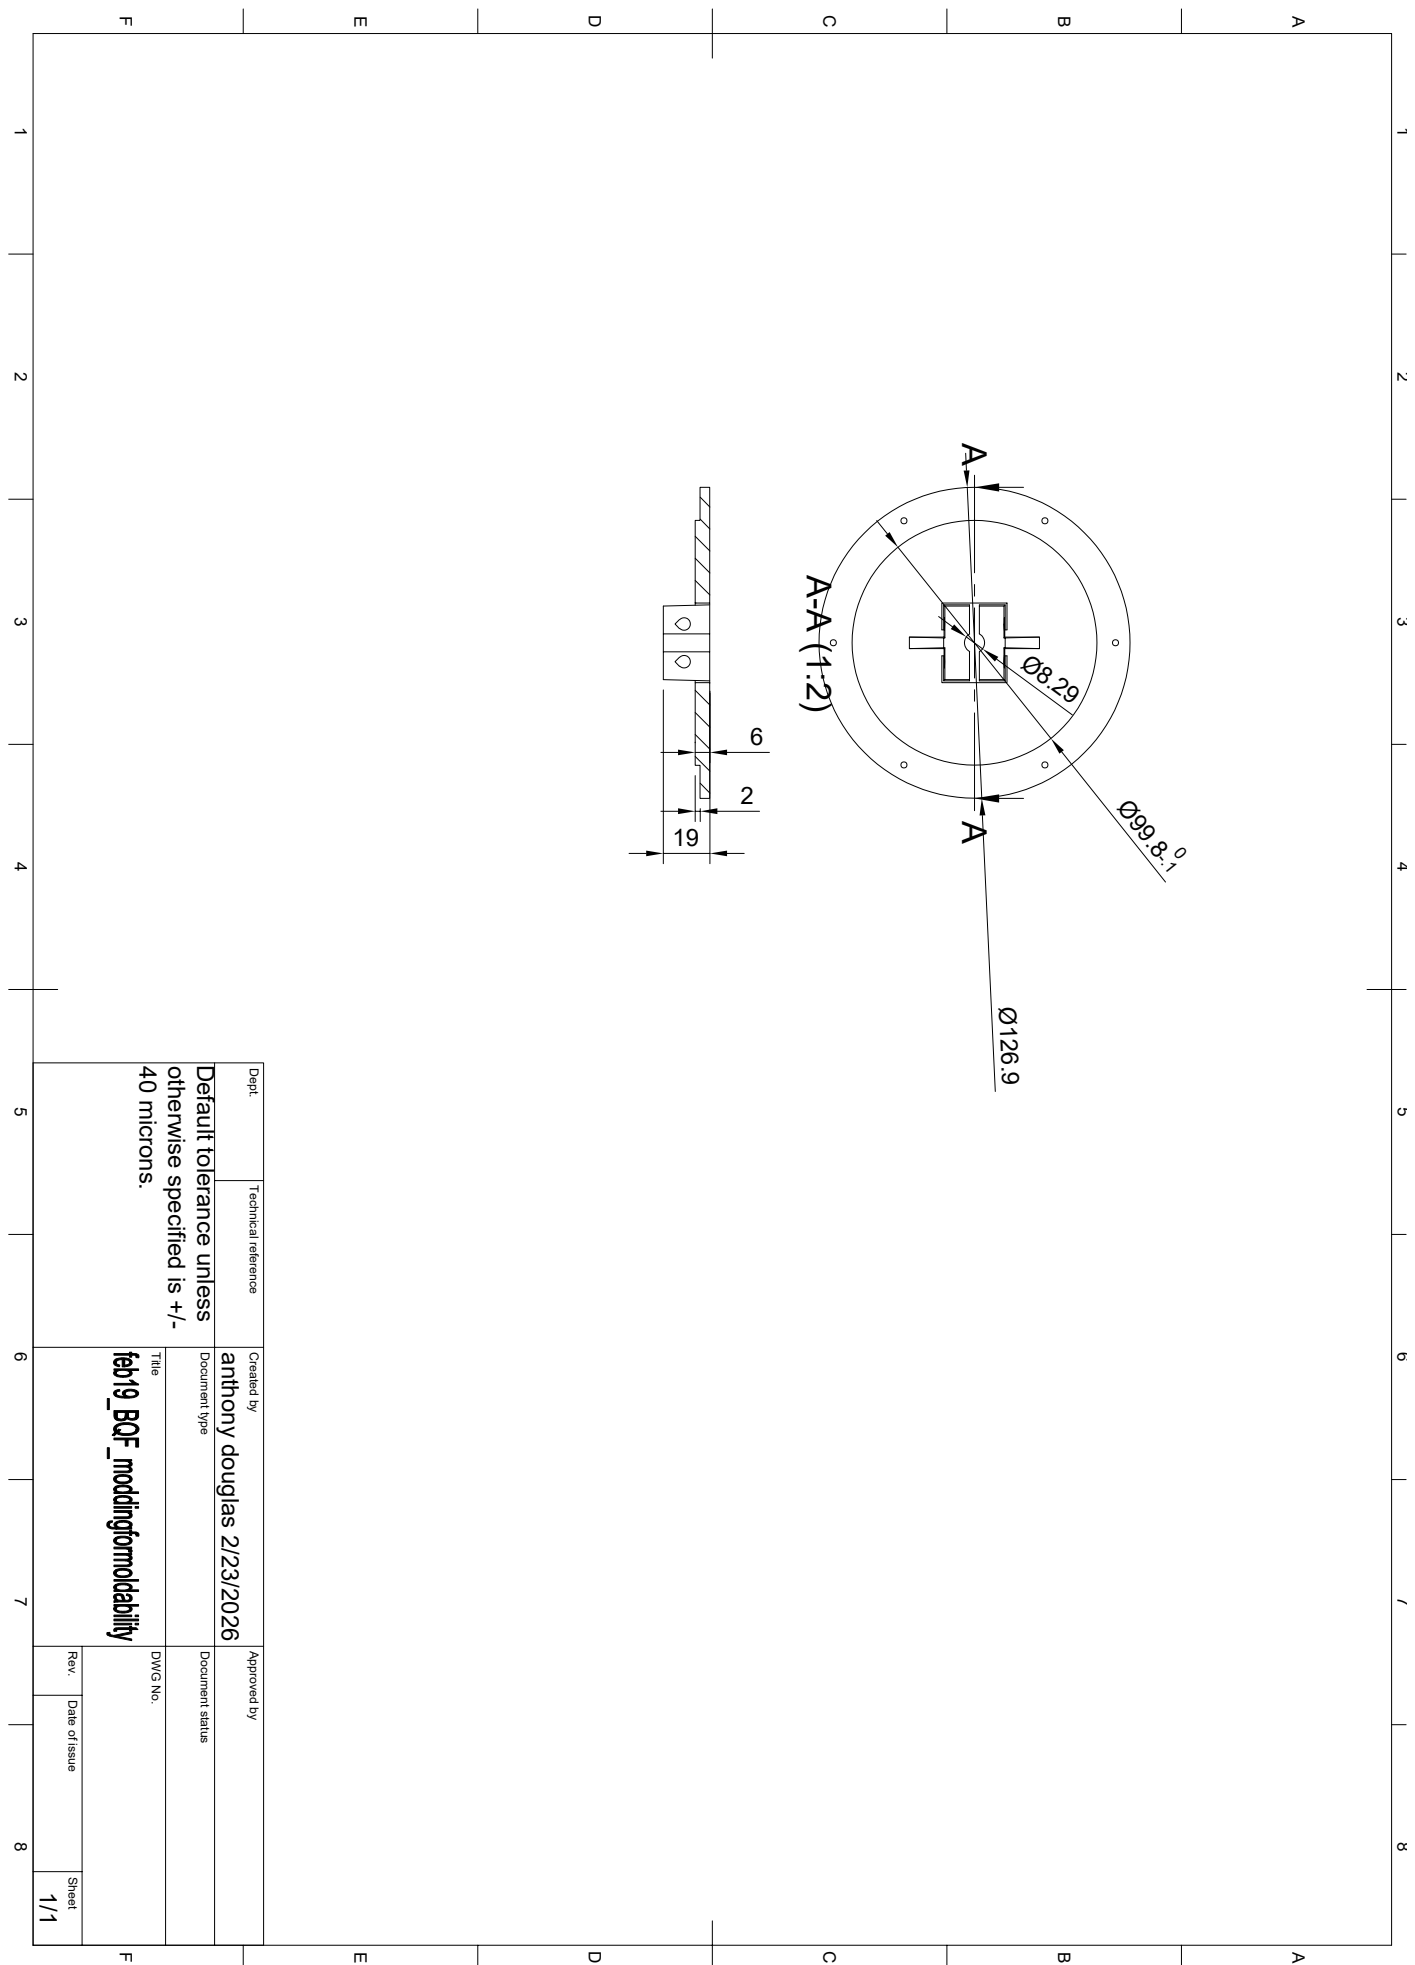
[picture p78: page 1]

1 A 2 3 4 5 6 7 8 1 2 3 4 5 6 7 8 FEDCB FEDCBA Dept. Technical reference Created by Approved by Title DWG No. Document type Document status Rev. Date of issue Sheet 2/23/2026 1/1 anthony douglas Ø99.8 0-.1 Ø8.29 40 microns. otherwise specified is +/- Default tolerance unless Ø126.9 A A A-A (1:2)
