adouglas89/Big-Quiet-Fan/dfm v1.0/main stuff for use by others/main manufacturing files/driver board/old/Schematic_stepperdrivertry4-2stdvr-copy_2025-11-27.pdf

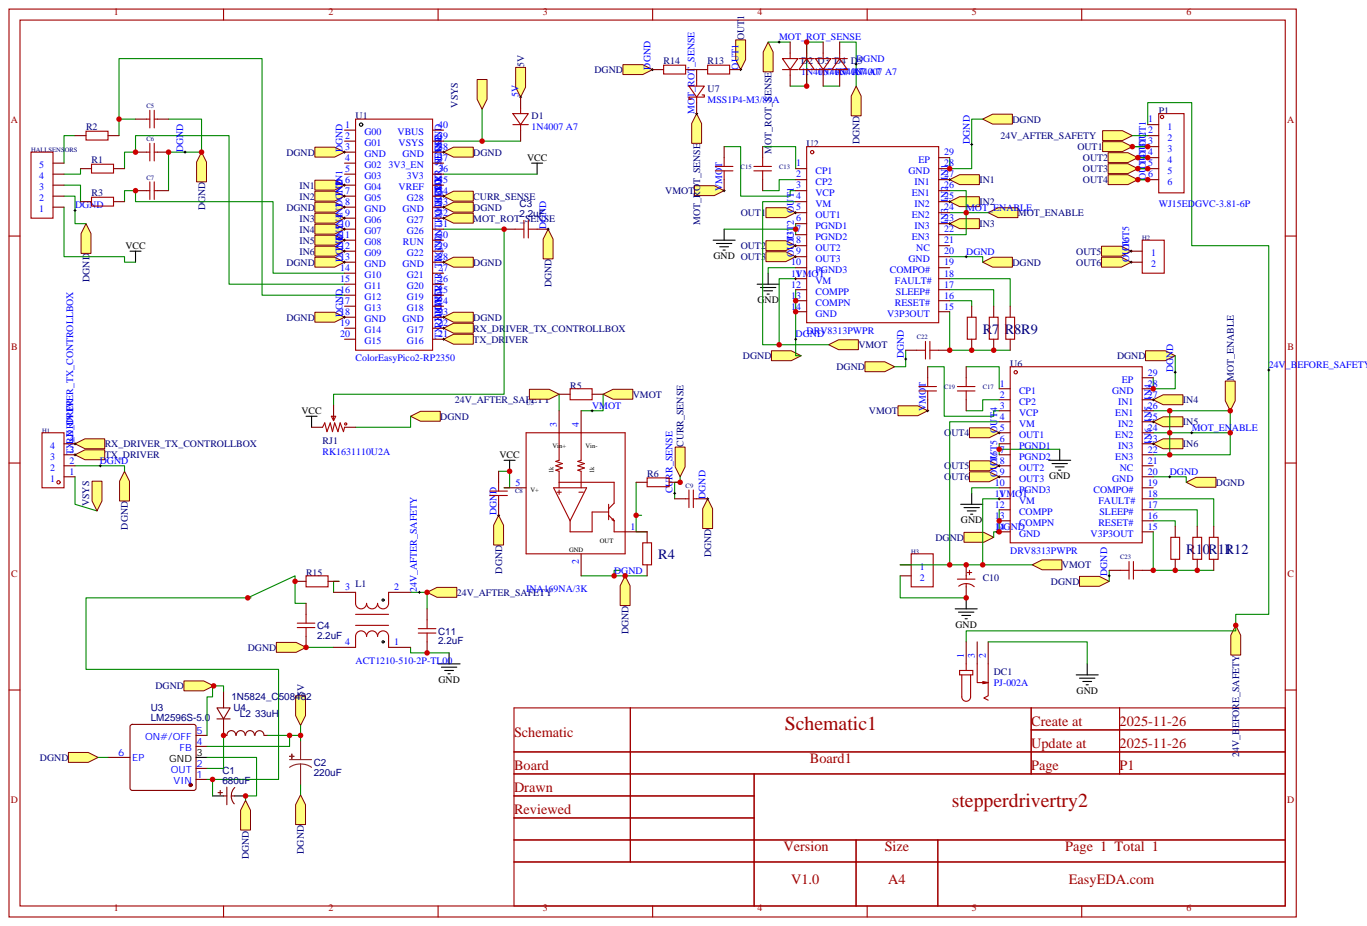
[picture p79: page 1]

Schematic | Schematic1 | Create at | 2025-11-26

Update at | 2025-11-26

Board | Board1 | Page | P1
Drawn | | stepperdrivertry2 Reviewed

Version | Size | Page 1 Total 1

V1.0 | A4 | EasyEDA.com
